myriadrf/front-end-modules/LimeSDR_PA_LNA/hardware/v1r3/KiCAD/Analog Circuits.sch

## KiCad design LimeSDR_PA_LNA/hardware/v1r3/KiCAD/Analog Circuits.sch (2016-06-01)

Schematic: Analog Circuits.sch

Parts:
R12: 10K_0402; SMD0402; Manufacturer Part Number RMCF0402FT10K0
R119, R120, R149, R150, R164, R165, R166, R167: 390R_0402; SMD0402; Manufacturer Part Number RMCF0402FT390R
U1: LMS7002; aQFN-261
X8, X9, X10, X11, X12, X13, X14, X15, X16, X17, X18, X19, X20, X21, X22, X23, X24, X25, X26, X27, X28, X29, X30, X31: U.FL; Manufacturer Part Number 0734120110
