myriadrf/front-end-modules/LimeSDR_PA_LNA/hardware/v1r3/KiCAD/Digital Circuits.sch

## KiCad design LimeSDR_PA_LNA/hardware/v1r3/KiCAD/Digital Circuits.sch (2016-06-01)

Schematic: Digital Circuits.sch

Parts:
C29, C161, C163: 1UF_0402; SMD0402; Manufacturer Part Number CC0402ZRY5V5BB105
C37: 100NF_0402; SMD0402; Manufacturer Part Number CC0402ZRY5V7BB104
C38: 100PF_0402; SMD0402; Manufacturer Part Number CC0402JRNPO9BN101
C119: 10PF_0402; SMD0402; Manufacturer Part Number CC0402JRNPO9BN100
C236, C237: 47PF_0402; SM0402; Manufacturer Part Number CC0402JRNPO9BN470
J1: FX10A-80P8; Manufacturer Part Number FX10B-80P/8-SV1(71)
J3: PINHEADER_2X5_TH; Pinhead_2x5_TH; Manufacturer Part Number 67996-412HLF
R9, R36, R63, R64, R65, R66: 47R_0402; SMD0402; Manufacturer Part Number RC0402FR-0747RL
R13, R37, R72: 10K_0402; SMD0402; Manufacturer Part Number RMCF0402FT10K0
R35, R38, R49: 0R_0402_NF; R_SM0402; Manufacturer Part Number RC0402JR-070RL
R39, R41, R42: 0R_0402; SMD0402; Manufacturer Part Number RC0402JR-070RL
R40, R44: 2K2_0402; SMD0402; Manufacturer Part Number RC0402FR-072K2L
TP1: TP
U1: LMS7002; aQFN-261
U2: CDCV304PWR; TSSOP-8; Manufacturer Part Number CDCV304PWR
U22: 24FC64F; 8-TSSOP; Manufacturer Part Number 24FC64F-I/ST
U23: 24FC512; 8-TSSOP; Manufacturer Part Number 24FC512-I/ST

Notes on the sheet:
+5V
