myriadrf/front-end-modules/LimeSDR_PA_LNA/hardware/v1r3/KiCAD/LMS7002 Power Supply.sch

## KiCad design LimeSDR_PA_LNA/hardware/v1r3/KiCAD/LMS7002 Power Supply.sch (2016-06-01)

Schematic: LMS7002 Power Supply.sch

Parts:
C30, C31, C32, C33, C36, C46, C47, C48, C49, C50, C51, C52, C53, C54, C55, C56, C57, C58, C59, C60, C62, C180, C181, C182, C183, C184, C185, C186, C188, C190, C192, C194, C220, C221, C222, C223, C224, C225: 1UF_0201; SM0201; Manufacturer Part Number C0603X5R0J105M030BC
FB1, FB2, FB3, FB4, FB5, FB6, FB7, FB8, FB10, FB11, FB12, FB13, FB14, FB22, FB28, FB30, FB32, FB34, FB36: FB_0201; SM0201; Manufacturer Part Number BK0603TS601-T
R2, R23, R146, R147, R148, R186: 0R_0201; SMD0201; Manufacturer Part Number MCR006YRTJ000
R48, R50: 0R_0402_NF; R_SM0402; Manufacturer Part Number RC0402JR-070RL
R61, R67, R68, R69, R70, R71: 10R_0201; SMD0201; Manufacturer Part Number RC0201JR-0710RP
R171, R172: 0.22R_0402; SMD0402; Manufacturer Part Number RL0402FR-070R22L
U1: LMS7002; aQFN-261
