myriadrf/front-end-modules/LimeSDR_PA_LNA/hardware/v1r3/KiCAD/Microcontroller.sch

## KiCad design LimeSDR_PA_LNA/hardware/v1r3/KiCAD/Microcontroller.sch (2016-06-01)

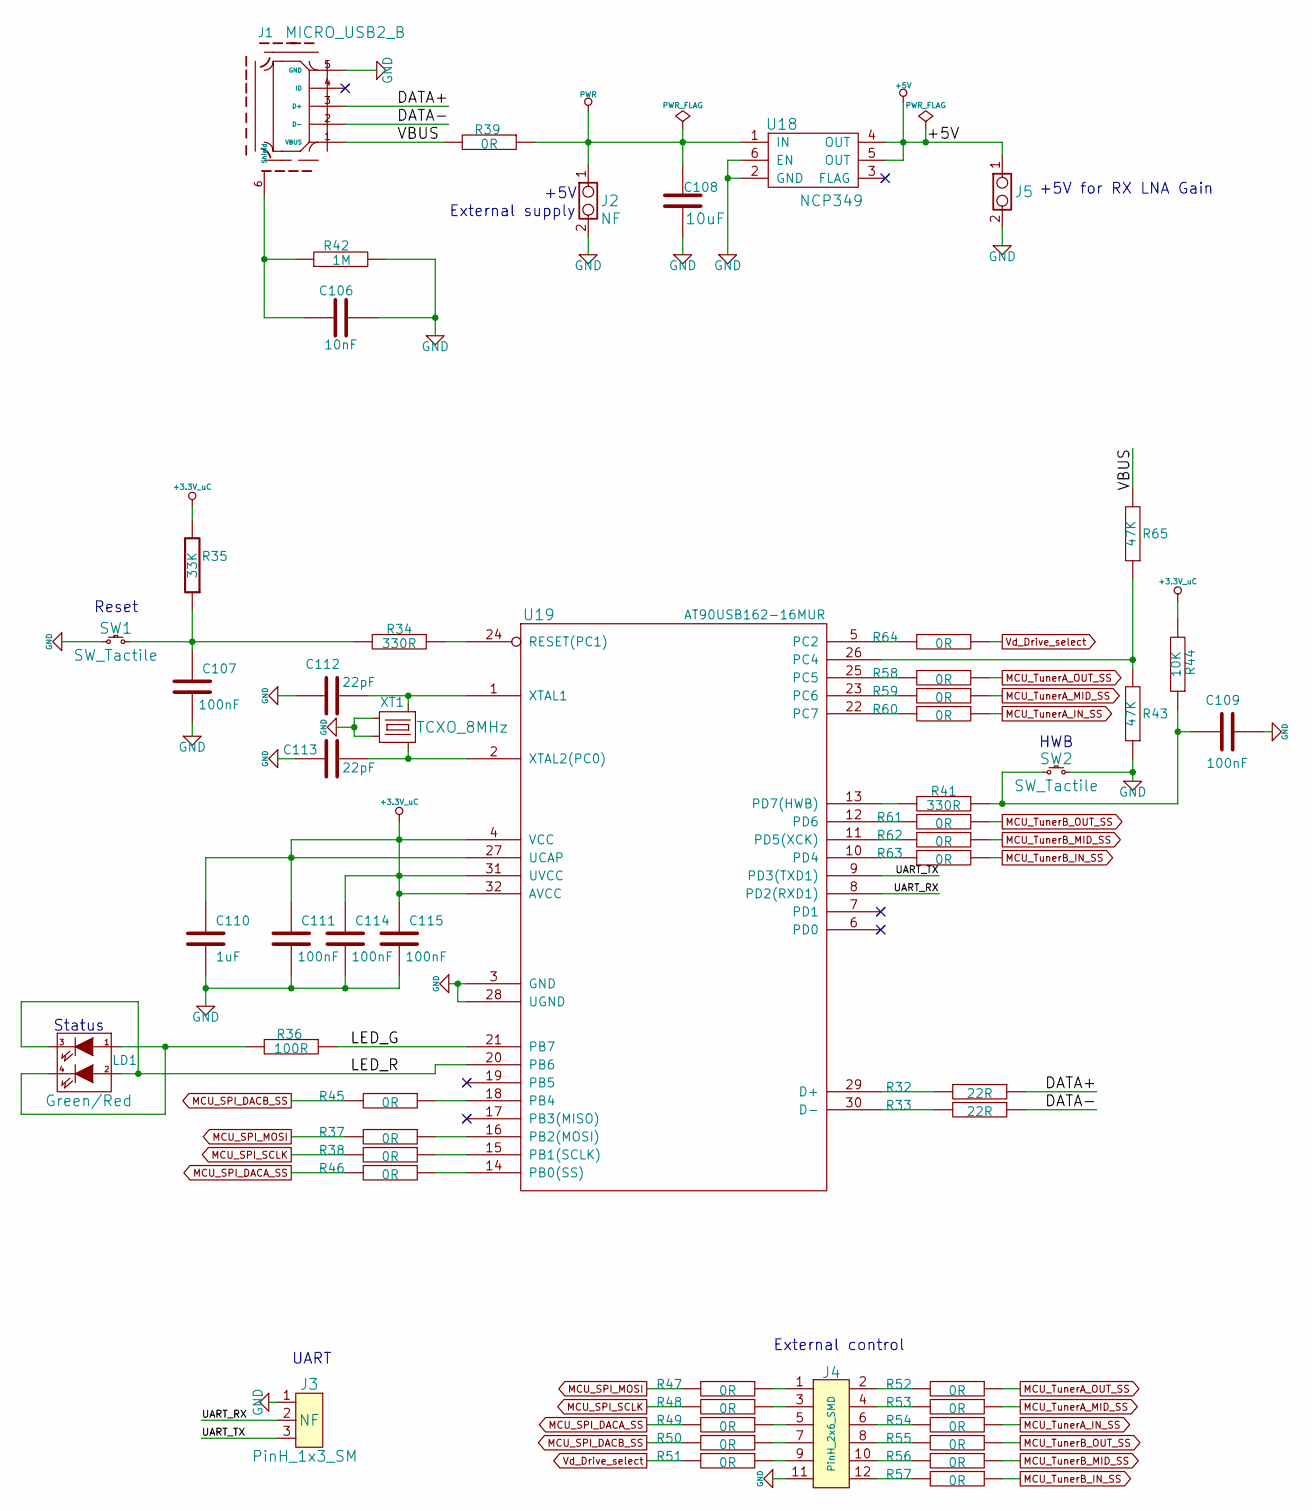
[picture p31: schematic Microcontroller.sch]

Parts:
C106: 10nF_0402; SM0402; Manufacturer Part Number CC0402KRX7R9BB103
C107, C109, C111, C114, C115: 100NF_0402; SMD0402; Manufacturer Part Number CC0402ZRY5V7BB104
C108: 10UF_1206; SMD1206; Manufacturer Part Number CC1206ZKY5V7BB106
C110: 1uF_0402; SMD0402; Manufacturer Part Number CC0402ZRY5V5BB105
C112, C113: 22pF_0402; SMD0402; Manufacturer Part Number CC0402JRNPO9BN220
J1: MICRO_USB2_B; microUSB2; Manufacturer Part Number 10118193-0001LF
J2: pinhead_2_NF; pinhead2; Manufacturer Part Number 5-146285-2
J3: PINHEADER_1X3_SM; Pinhead_1x3_SM; Manufacturer Part Number GRPB031VWTC-RC
J4: Pinheader_2x6_SMD_1.27; Pinhead_2x6_SMD; Manufacturer Part Number M50-3600642
J5: pinhead_2; pinhead2; Manufacturer Part Number 5-146285-2
LD1: LED_0603_GR; LD_0603; Manufacturer Part Number HSMF-C165
R32, R33: 22R_0402; SMD0402; Manufacturer Part Number RC0402JR-0722RL
R34, R41: 330R_0402; SMD0402; Manufacturer Part Number RC0402JR-07330RL
R35: 33K_0402; R_SM0402; Manufacturer Part Number RC0402FR-0733KL
R36: 100R_0402; SMD0402; Manufacturer Part Number RC0603JR-07100RL
R37, R38, R39, R45, R46, R47, R48, R49, R50, R51, R52, R53, R54, R55, R56, R57, R58, R59, R60, R61, R62, R63, R64: 0R_0402; SMD0402; Manufacturer Part Number RC0402JR-070RL
R42: 1M_0402; R_SM0402; Manufacturer Part Number RC0402FR-071ML
R43, R65: 47K_0402; SMD0402; Manufacturer Part Number RC0402FR-0747KL
R44: 10K_0402; SMD0402; Manufacturer Part Number RMCF0402FT10K0
SW1, SW2: SW_Tactile; SW_B3U-1000P; Manufacturer Part Number B3U-1000P
U18: NCP349; 6-DFN; Manufacturer Part Number NCP349MNAETBG
U19: AT90USB162-16MUR; VQFN32; Manufacturer Part Number AT90USB162-16MUR
XT1: TCXO_8MHz; XO_4DFN; Manufacturer Part Number ABM3B-8.000MHZ-B2-T

Connections:
+3.3V_uC: C110.1, C111.1, C114.1, C115.1, R35.2, R44.2, U19.4 (VCC), U19.27 (UCAP), U19.31 (UVCC), U19.32 (AVCC)
+5V: J5.1, U18.4 (OUT), U18.5 (OUT)
DATA+: J1.3 (D+), R32.1
DATA-: J1.2 (D-), R33.1
GND: C106.2, C107.2, C108.2, C109.2, C110.2, C111.2, C112.1, C113.1, C114.2, C115.2, J1.5 (GND), J2.2, J3.1, J4.11, J5.2, R42.2, R43.1, SW1.1 (Base), SW2.2 (Coll), U18.2 (GND), U18.6 (EN), U19.3 (GND), U19.28 (UGND), XT1.2, XT1.4
LED_G: R36.1, U19.21 (PB7)
LED_R: LD1.2 (A), LD1.3 (K), U19.20 (PB6)
MCU_SPI_DACA_SS: R46.2, R49.2
MCU_SPI_DACB_SS: R45.2, R50.2
MCU_SPI_MOSI: R37.2, R47.2
MCU_SPI_SCLK: R38.2, R48.2
MCU_TunerA_IN_SS: R54.1, R60.1
MCU_TunerA_MID_SS: R53.1, R59.1
MCU_TunerA_OUT_SS: R52.1, R58.1
MCU_TunerB_IN_SS: R57.1, R63.1
MCU_TunerB_MID_SS: R56.1, R62.1
MCU_TunerB_OUT_SS: R55.1, R61.1
unnamed: C106.1, J1.6 (Shield), R42.1
unnamed: C107.1, R34.2, R35.1, SW1.2 (Coll)
unnamed: C109.1, R41.1, R44.1, SW2.1 (Base)
unnamed: C112.2, U19.1 (XTAL1), XT1.3
unnamed: C113.2, U19.2 (XTAL2(PC0)), XT1.1
unnamed: J4.1, R47.1
unnamed: J4.2, R52.2
unnamed: J4.3, R48.1
unnamed: J4.4, R53.2
unnamed: J4.5, R49.1
unnamed: J4.6, R54.2
unnamed: J4.7, R50.1
unnamed: J4.8, R55.2
unnamed: J4.9, R51.1
unnamed: J4.10, R56.2
unnamed: J4.12, R57.2
unnamed: LD1.1 (A), LD1.4 (K), R36.2
unnamed: R32.2, U19.29 (D+)
unnamed: R33.2, U19.30 (D-)
unnamed: R34.1, U19.24 (RESET(PC1))
unnamed: R37.1, U19.16 (PB2(MOSI))
unnamed: R38.1, U19.15 (PB1(SCLK))
unnamed: R41.2, U19.13 (PD7(HWB))
unnamed: R43.2, R65.1, U19.26 (PC4)
unnamed: R45.1, U19.18 (PB4)
unnamed: R46.1, U19.14 (PB0(SS))
unnamed: R58.2, U19.25 (PC5)
unnamed: R59.2, U19.23 (PC6)
unnamed: R60.2, U19.22 (PC7)
unnamed: R61.2, U19.12 (PD6)
unnamed: R62.2, U19.11 (PD5(XCK))
unnamed: R63.2, U19.10 (PD4)
unnamed: R64.2, U19.5 (PC2)
PWR: C108.1, J2.1, R39.1, U18.1 (IN)
UART_RX: J3.2, U19.8 (PD2(RXD1))
UART_TX: J3.3, U19.9 (PD3(TXD1))
VBUS: J1.1 (VBUS), R39.2, R65.2
Vd_Drive_select: R51.2, R64.1

Notes on the sheet:
+5V
Status
External control
External supply
UART
Reset
+5V for RX LNA Gain
HWB
