myriadrf/front-end-modules/LimeSDR_PA_LNA/hardware/v1r3/KiCAD/Power Supply.sch

## KiCad design LimeSDR_PA_LNA/hardware/v1r3/KiCAD/Power Supply.sch (2016-06-01)

Schematic: Power Supply.sch

Parts:
C9, C10, C11, C12, C13, C14, C16, C18, C24, C29: 1UF_0402; SMD0402; Manufacturer Part Number CC0402ZRY5V5BB105
C15, C23: 10UF_0402; SMD0402; Manufacturer Part Number CL05A106MP5NUNC
C17, C25, C28: 100NF_0402; SMD0402; Manufacturer Part Number CC0402ZRY5V7BB104
C19, C20, C21, C22, C26, C27, C30, C31: 2.2UF_0603; SMD0603; Manufacturer Part Number CC0603ZRY5V6BB225
FB1, FB2, FB3: FB_60R_0805; FB_SM0805; Manufacturer Part Number MMZ2012Y600B
FD1, FD2, FD3, FD4, FD5, FD6: FIDUCIAL; Fiducial
R1, R10, R22: 10K_0402; SMD0402; Manufacturer Part Number RMCF0402FT10K0
R2, R6: 200R_0402; R_SM0402; Manufacturer Part Number RC0402FR-07200RL
R3, R4, R23: 1K_0402; SMD0402; Manufacturer Part Number RMCF0402FT1K00
R5, R11, R12, R13, R20, R30: 0R_0402; SM0402; Manufacturer Part Number CRCW04020000Z0ED
R7, R8: 2K32_0402; SM0402; Manufacturer Part Number RMCF0402FT2K32
R9, R21: 0R_0402_NF; R_SM0402; Manufacturer Part Number RC0402JR-070RL
R14, R15, R16, R25, R26, R27: 15K_0402; R_SM0402; Manufacturer Part Number RC0402FR-0715KL
R17, R18, R19, R28, R29, R31: 4K3_0402; R_SM0402; Manufacturer Part Number RC0402JR-074K3L
R24: 806R_0402; SM0402; Manufacturer Part Number RMCF0402FT806R
U3, U7: AD5601B; SC-70-6; Manufacturer Part Number AD5601BKSZ-REEL7
U4, U5, U6, U8: MIC37122YMT_ADJ_6TMLF; 6TMLF; Manufacturer Part Number MIC37122YMT-TR
U9: POWERSWITCH_2:1; 6-UFBGA; Manufacturer Part Number FPF1320UCX

Notes on the sheet:
(3.3V)
VDAC_A - Vg_A 1.13V - 0.25V 1.55V - 0.35V 2.00V - 0.45V
Vd Drive - VOUT 0 - 5V 1 - 2V
VDAC_B - Vg _B 1.13V - 0.25V 1.55V - 0.35V 2.00V - 0.45V
VDAC_A
VDAC_B
