myriadrf/front-end-modules/LimeSDR_PA_LNA/hardware/v1r3/KiCAD/RF1.sch

## KiCad design LimeSDR_PA_LNA/hardware/v1r3/KiCAD/RF1.sch (2016-06-01)

Schematic: RF1.sch

Parts:
C1, C9, C10, C11, C13, C121, C166: 100NF_0402; SMD0402; Manufacturer Part Number CC0402ZRY5V7BB104
C2, C7, C20, C24, C34: 1PF_0402; SMD0402; Manufacturer Part Number C1005C0G1H010B050BA
C3, C21: 100PF_0402; SMD0402; Manufacturer Part Number CC0402JRNPO9BN101
C6, C35, C235: 0.5PF_0402_NF; SMD0402; Manufacturer Part Number CC0402CRNPO9BNR50
C12: 1PF_0402_NF; SMD0402; Manufacturer Part Number C1005C0G1H010B050BA
C14, C18, C26, C27: 220PF_0402; SMD0402; Manufacturer Part Number CC0402KRX7R9BB221
C15, C28: 470PF_0402; SMD0402; Manufacturer Part Number C1005C0G1H471J050BA
C67, C69: 1.5PF_0402; SMD0402; Manufacturer Part Number C1005C0G1H1R5B050BA
C68: 0.5PF_0402; SMD0402; Manufacturer Part Number CC0402CRNPO9BNR50
L1, L2, L9: 8.2NH_0402; IND_0402; Manufacturer Part Number 0402HP-8N2XJLU
L6, L7: 270NH_0402; IND_0402; Manufacturer Part Number 0402HL-271XJRU
L13: 12NH_0402_NF; IND_0402; Manufacturer Part Number 0402HP-12NX_LU
L14, L15: 100UH_0805; SM0805; Manufacturer Part Number MLF2012C101K
L17: 4.7NH_0402; IND_0402; Manufacturer Part Number 0402HP-4N7X_LU
T1, T2, T3, T5: TR_TC1; TC1-1-13MA+; Manufacturer Part Number TC1-1-13MA+
T4: TR_TCM1-43X+; TCM1-43X+; Manufacturer Part Number TCM1-43X+
U1: LMS7002; aQFN-261; Manufacturer Part Number LMS7002M

Notes on the sheet:
LNAW_A
LNAL_A
LNAH_A
TX2_A
TX1_A
Broadband
High Band
Low Band
Broadband
