myriadrf/front-end-modules/LimeSDR_PA_LNA/hardware/v1r3/KiCAD/RF2.sch

## KiCad design LimeSDR_PA_LNA/hardware/v1r3/KiCAD/RF2.sch (2016-06-01)

Schematic: RF2.sch

Parts:
C4, C5, C8, C16, C25, C45, C86: 100NF_0402; SMD0402; Manufacturer Part Number CC0402ZRY5V7BB104
C17: 1PF_0402_NF; SMD0402; Manufacturer Part Number C1005C0G1H010B050BA
C19, C82, C238: 0.5PF_0402_NF; SMD0402; Manufacturer Part Number CC0402CRNPO9BNR50
C22, C23, C74, C78, C81: 1PF_0402; SMD0402; Manufacturer Part Number C1005C0G1H010B050BA
C72, C73, C79, C80: 220PF_0402; SMD0402; Manufacturer Part Number CC0402KRX7R9BB221
C83, C85: 1.5PF_0402; SMD0402; Manufacturer Part Number C1005C0G1H1R5B050BA
C84: 0.5PF_0402; SMD0402; Manufacturer Part Number CC0402CRNPO9BNR50
C87, C89: 100PF_0402; SMD0402; Manufacturer Part Number CC0402JRNPO9BN101
C88, C90: 470PF_0402; SMD0402; Manufacturer Part Number C1005C0G1H471J050BA
L3, L5, L10: 8.2NH_0402; IND_0402; Manufacturer Part Number 0402HP-8N2XJLU
L4, L8: 270NH_0402; IND_0402; Manufacturer Part Number 0402HL-271XJRU
L11: 12NH_0402_NF; IND_0402; Manufacturer Part Number 0402HP-12NX_LU
L12: 4.7NH_0402; IND_0402; Manufacturer Part Number 0402HP-4N7X_LU
L16, L18: 100UH_0805; SM0805; Manufacturer Part Number MLF2012C101K
T6, T7, T8, T10: TR_TC1; TC1-1-13MA+; Manufacturer Part Number TC1-1-13MA+
T9: TR_TCM1-43X+; TCM1-43X+; Manufacturer Part Number TCM1-43X+
U1: LMS7002; aQFN-261

Notes on the sheet:
LNAW_B
LNAL_B
LNAH_B
TX2_B
TX1_B
Broadband
High Band
Low Band
Broadband
Low Band
