myriadrf/front-end-modules/LimeSDR_PA_LNA/hardware/v1r3/KiCAD/RX_LNA chain.sch

## KiCad design LimeSDR_PA_LNA/hardware/v1r3/KiCAD/RX_LNA chain.sch (2016-06-01)

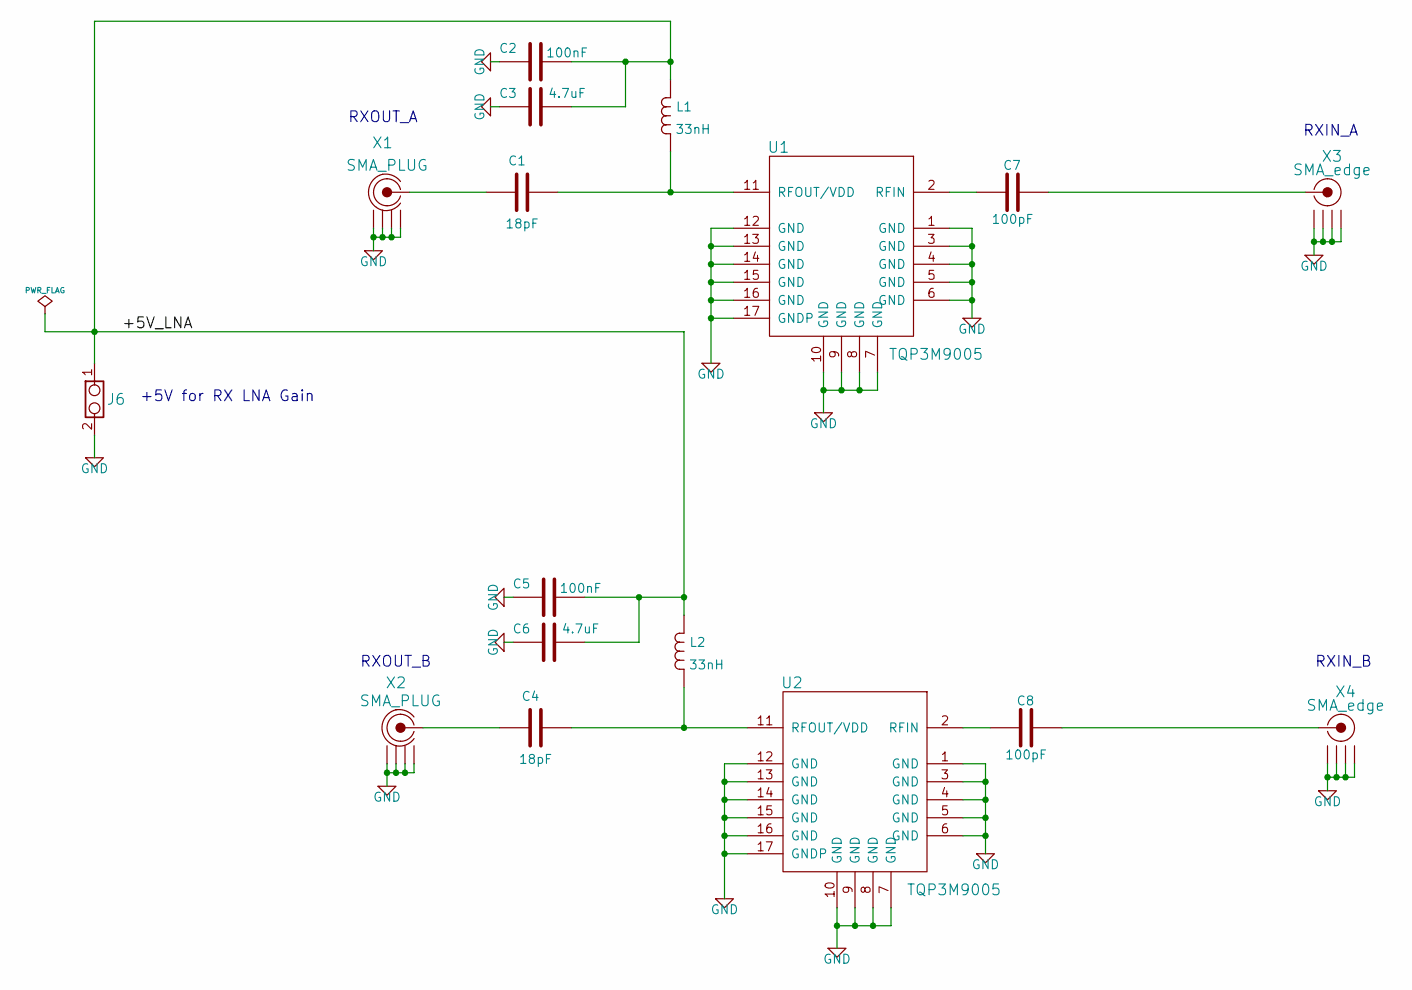
[picture p32: schematic RX_LNA chain.sch]

Parts:
C1, C4: 18PF_0402; SM0402; Manufacturer Part Number CC0402JRNPO9BN180
C2, C5: 100NF_0402; SMD0402; Manufacturer Part Number CC0402ZRY5V7BB104
C3, C6: 4.7UF_0402; SM0402; Manufacturer Part Number C1005X5R0J475M050BC
C7, C8: 100PF_0402; SMD0402; Manufacturer Part Number CC0402JRNPO9BN101
J6: pinhead_2; pinhead2; Manufacturer Part Number 5-146285-2
L1, L2: 33NH_0402; SM0402; Manufacturer Part Number 0402CS-33NX_LU
U1, U2: TQP3M9005; QFN16_LNA; Manufacturer Part Number TQP3M9005
X1, X2: SMA_PLUG; SMA; Manufacturer Part Number CONSMA013.062
X3, X4: SMA_edge; Manufacturer Part Number 142-0711-821

Connections:
+5V_LNA: C2.2, C3.2, C5.2, C6.2, J6.1, L1.1, L2.1
GND: C2.1, C3.1, C5.1, C6.1, J6.2, U1.1 (GND), U1.3 (GND), U1.4 (GND), U1.5 (GND), U1.6 (GND), U1.7 (GND), U1.8 (GND), U1.9 (GND), U1.10 (GND), U1.12 (GND), U1.13 (GND), U1.14 (GND), U1.15 (GND), U1.16 (GND), U1.17 (GNDP), U2.1 (GND), U2.3 (GND), U2.4 (GND), U2.5 (GND), U2.6 (GND), U2.7 (GND), U2.8 (GND), U2.9 (GND), U2.10 (GND), U2.12 (GND), U2.13 (GND), U2.14 (GND), U2.15 (GND), U2.16 (GND), U2.17 (GNDP), X1.2 (GND1), X1.3 (GND2), X1.4 (GND3), X1.5 (GND4), X2.2 (GND1), X2.3 (GND2), X2.4 (GND3), X2.5 (GND4), X3.2 (GND1), X3.3 (GND2), X3.4 (GND3), X3.5 (GND4), X4.2 (GND1), X4.3 (GND2), X4.4 (GND3), X4.5 (GND4)
unnamed: C1.1, X1.1 (RF)
unnamed: C1.2, L1.2, U1.11 (RFOUT/VDD)
unnamed: C4.1, X2.1 (RF)
unnamed: C4.2, L2.2, U2.11 (RFOUT/VDD)
unnamed: C7.1, U1.2 (RFIN)
unnamed: C7.2, X3.1 (RF)
unnamed: C8.1, U2.2 (RFIN)
unnamed: C8.2, X4.1 (RF)

Notes on the sheet:
RXOUT_A
RXOUT_B
RXIN_A
RXIN_B
+5V for RX LNA Gain
