myriadrf/front-end-modules/LimeSDR_PA_LNA/hardware/v1r3/KiCAD/TX_A PA chain.sch

## KiCad design LimeSDR_PA_LNA/hardware/v1r3/KiCAD/TX_A PA chain.sch (2016-06-01)

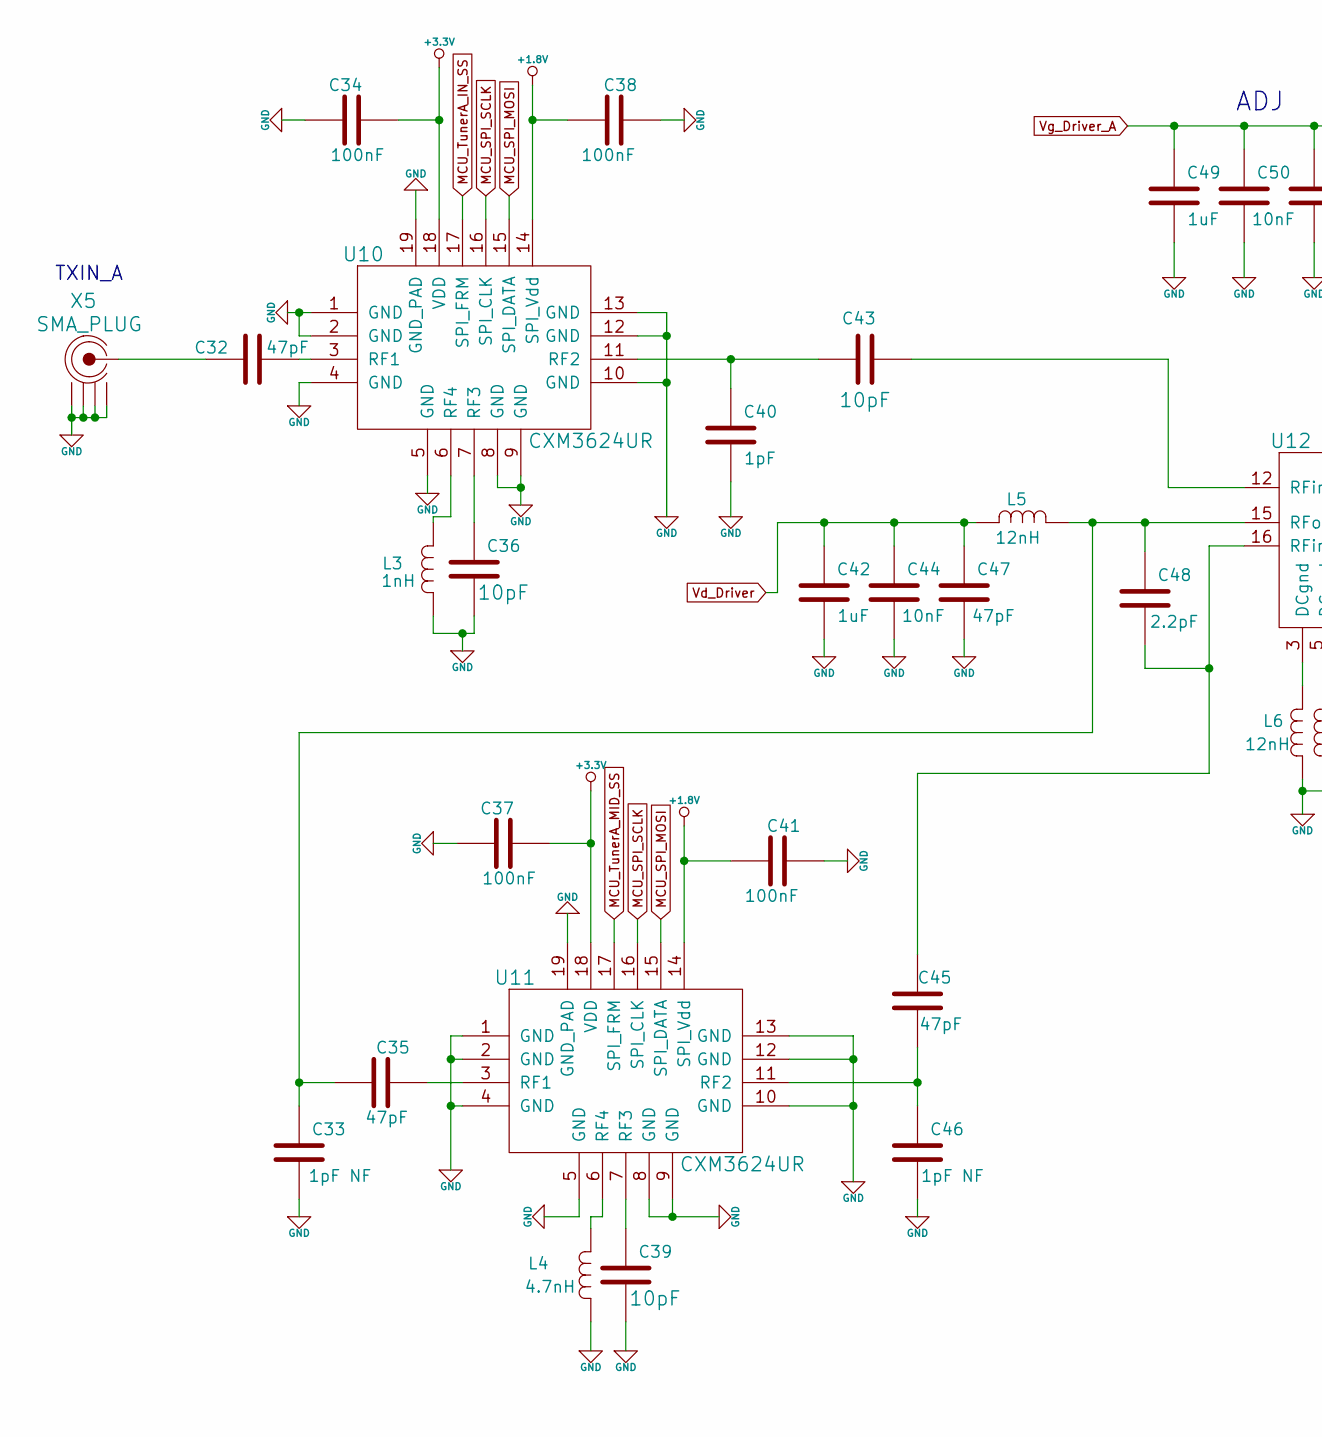
[picture p33: schematic TX_A PA chain.sch, part in row 1, column 1]

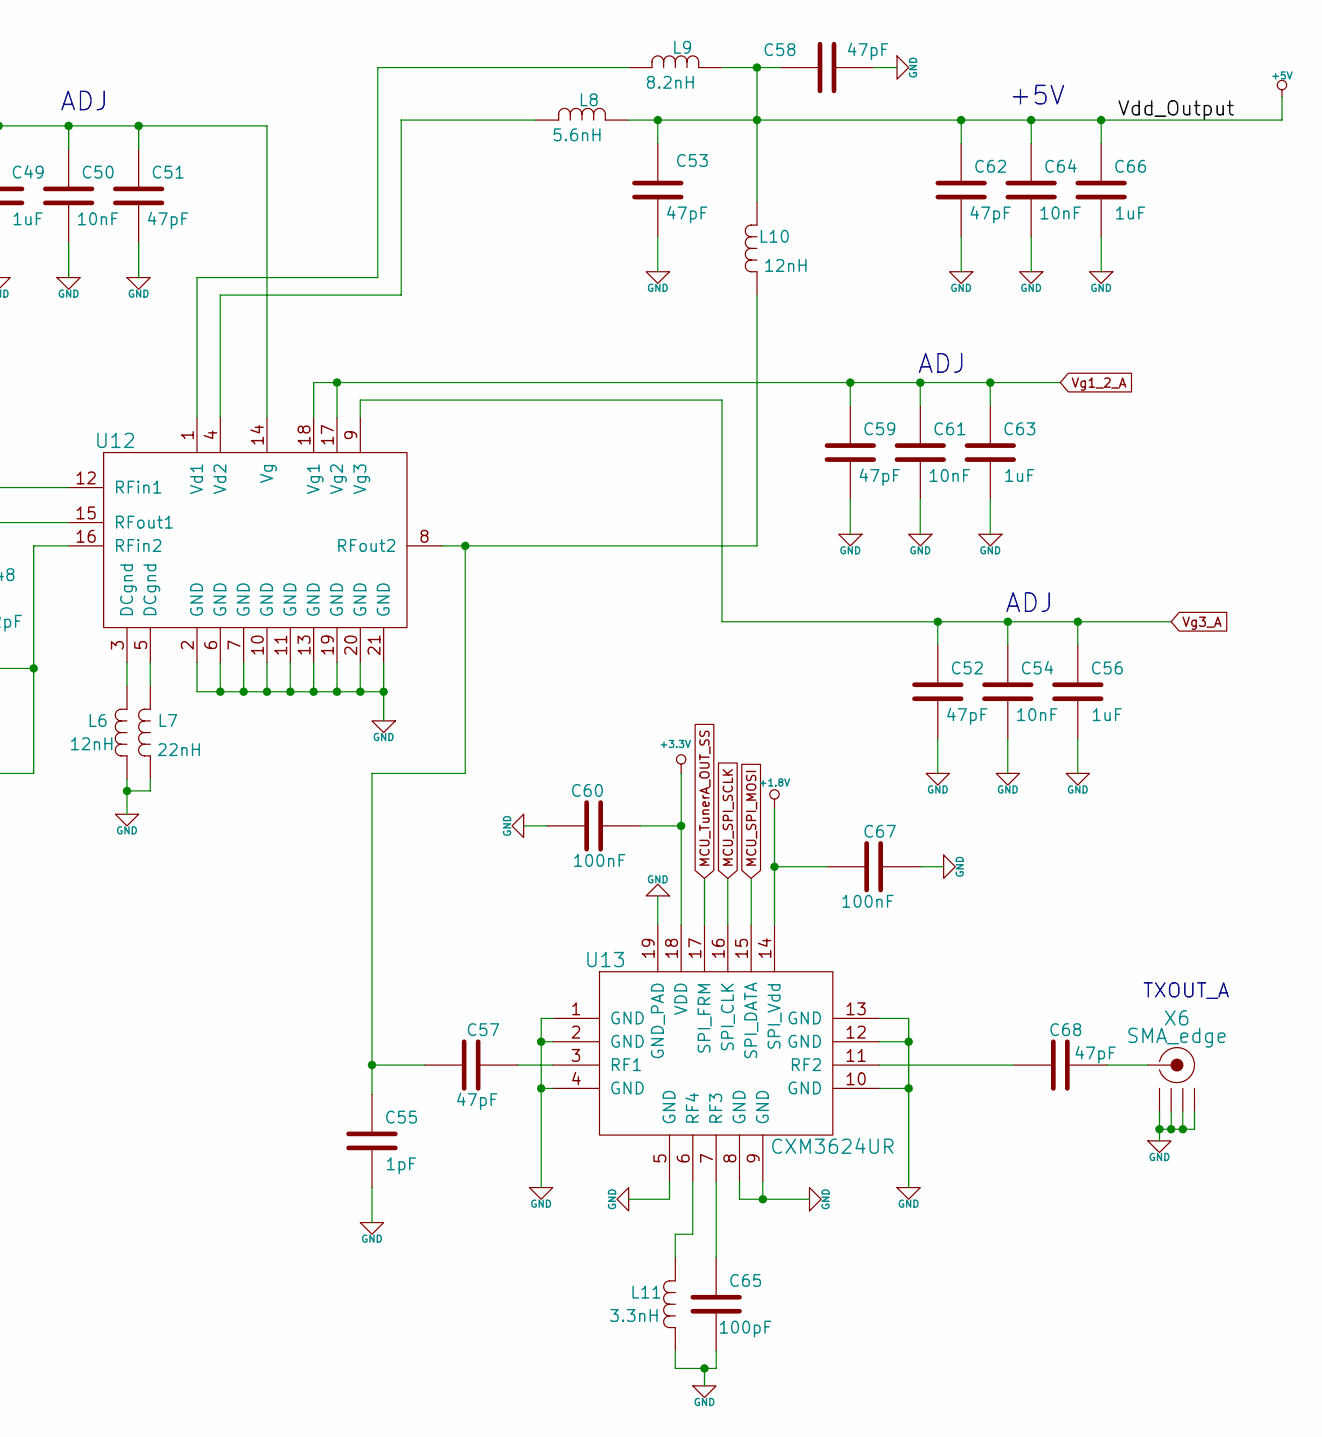
[picture p34: schematic TX_A PA chain.sch, part in row 1, column 2]

Parts:
C32, C35, C47, C51, C52, C53, C57, C58, C59, C62, C68: 47PF_0402; SM0402; Manufacturer Part Number CC0402JRNPO9BN470
C33, C46: 1PF_0402_NF; SMD0402; Manufacturer Part Number C1005C0G1H010B050BA
C34, C37, C38, C41, C60, C67: 100NF_0402; SMD0402; Manufacturer Part Number CC0402ZRY5V7BB104
C36, C39, C43: 10pF_0402; SMD0402; Manufacturer Part Number CC0402JRNPO9BN100
C40, C55: 1PF_0402; SMD0402; Manufacturer Part Number C1005C0G1H010B050BA
C42, C49, C56, C63, C66: 1UF_0402; SMD0402; Manufacturer Part Number CC0402ZRY5V5BB105
C44, C50, C54, C61, C64: 10NF_0402; SM0402; Manufacturer Part Number CC0402KRX7R9BB103
C45: 47pF_0402; SM0402; Manufacturer Part Number CC0402JRNPO9BN470
C48: 2.2pF_0402; SMD0402; Manufacturer Part Number C1005NP01H2R2C050BA
C65: 100pF_0402; SMD0402; Manufacturer Part Number CC0402JRNPO9BN101
L3: 1.0nH_0402; L_SM0402; Manufacturer Part Number 0402HP-1N0XJLU
L4: 4.7NH_0402; IND_0402; Manufacturer Part Number 0402HP-4N7X_LU
L5, L6, L10: 12NH_0402; SM0402; Manufacturer Part Number 0402HP-12NX_LU
L7: 22NH_0402; L_SM0402; Manufacturer Part Number 0402HP-22NX_LU
L8: 5.6NH_0402; L_SM0402; Manufacturer Part Number 0402HP-5N6XJLU
L9: 8.2NH_0402; IND_0402; Manufacturer Part Number 0402HP-8N2X_LU
L11: 3.3nH_0402; L_SM0402; Manufacturer Part Number 0402HP-3N3X_LU
U10, U11, U13: CXM3624UR; UQFN_18P; Manufacturer Part Number CXM3624UR
U12: CXGXXXX; 20PIN-VQFN
X5: SMA_PLUG; SMA; Manufacturer Part Number CONSMA013.062
X6: SMA_edge; Manufacturer Part Number 142-0711-821

Connections:
+1.8V: C38.2, C41.2, C67.2, U10.14 (SPI_Vdd), U11.14 (SPI_Vdd), U13.14 (SPI_Vdd)
+3.3V: C34.2, C37.2, C60.2, U10.18 (VDD), U11.18 (VDD), U13.18 (VDD)
+5V: C53.2, C58.1, C62.1, C64.1, C66.1, L8.1, L9.1, L10.1
GND: C33.2, C34.1, C36.2, C37.1, C38.1, C39.2, C40.2, C41.1, C42.2, C44.2, C46.2, C47.2, C49.2, C50.2, C51.2, C52.2, C53.1, C54.2, C55.2, C56.2, C58.2, C59.2, C60.1, C61.2, C62.2, C63.2, C64.2, C65.2, C66.2, C67.1, L3.2, L4.2, L6.2, L7.2, L11.2, U10.1 (GND), U10.2 (GND), U10.4 (GND), U10.5 (GND), U10.8 (GND), U10.9 (GND), U10.10 (GND), U10.12 (GND), U10.13 (GND), U10.19 (GND_PAD), U11.1 (GND), U11.2 (GND), U11.4 (GND), U11.5 (GND), U11.8 (GND), U11.9 (GND), U11.10 (GND), U11.12 (GND), U11.13 (GND), U11.19 (GND_PAD), U12.2 (GND), U12.6 (GND), U12.7 (GND), U12.10 (GND), U12.11 (GND), U12.13 (GND), U12.19 (GND), U12.20 (GND), U12.21 (GND), U13.1 (GND), U13.2 (GND), U13.4 (GND), U13.5 (GND), U13.8 (GND), U13.9 (GND), U13.10 (GND), U13.12 (GND), U13.13 (GND), U13.19 (GND_PAD), X5.2 (GND1), X5.3 (GND2), X5.4 (GND3), X5.5 (GND4), X6.2 (GND1), X6.3 (GND2), X6.4 (GND3), X6.5 (GND4)
MCU_SPI_MOSI: U10.15 (SPI_DATA), U11.15 (SPI_DATA), U13.15 (SPI_DATA)
MCU_SPI_SCLK: U10.16 (SPI_CLK), U11.16 (SPI_CLK), U13.16 (SPI_CLK)
MCU_TunerA_IN_SS: U10.17 (SPI_FRM)
MCU_TunerA_MID_SS: U11.17 (SPI_FRM)
MCU_TunerA_OUT_SS: U13.17 (SPI_FRM)
unnamed: C32.1, X5.1 (RF)
unnamed: C32.2, U10.3 (RF1)
unnamed: C33.1, C35.2, C48.1, L5.1, U12.15 (RFout1)
unnamed: C35.1, U11.3 (RF1)
unnamed: C36.1, U10.7 (RF3)
unnamed: C39.1, U11.7 (RF3)
unnamed: C40.1, C43.1, U10.11 (RF2)
unnamed: C43.2, U12.12 (RFin1)
unnamed: C45.1, C46.1, U11.11 (RF2)
unnamed: C45.2, C48.2, U12.16 (RFin2)
unnamed: C55.1, C57.2, L10.2, U12.8 (RFout2)
unnamed: C57.1, U13.3 (RF1)
unnamed: C65.1, U13.7 (RF3)
unnamed: C68.1, U13.11 (RF2)
unnamed: C68.2, X6.1 (RF)
unnamed: L3.1, U10.6 (RF4)
unnamed: L4.1, U11.6 (RF4)
unnamed: L6.1, U12.3 (DCgnd)
unnamed: L7.1, U12.5 (DCgnd)
unnamed: L8.2, U12.4 (Vd2)
unnamed: L9.2, U12.1 (Vd1)
unnamed: L11.1, U13.6 (RF4)
Vd_Driver: C42.1, C44.1, C47.1, L5.2
Vg1_2_A: C59.1, C61.1, C63.1, U12.17 (Vg2), U12.18 (Vg1)
Vg3_A: C52.1, C54.1, C56.1, U12.9 (Vg3)
Vg_Driver_A: C49.1, C50.1, C51.1, U12.14 (Vg)

Notes on the sheet:
ADJ
+5V
TXOUT_A
TXIN_A
