myriadrf/front-end-modules/LimeSDR_PA_LNA/hardware/v1r3/KiCAD/TX_B PA chain.sch

## KiCad design LimeSDR_PA_LNA/hardware/v1r3/KiCAD/TX_B PA chain.sch (2016-06-01)

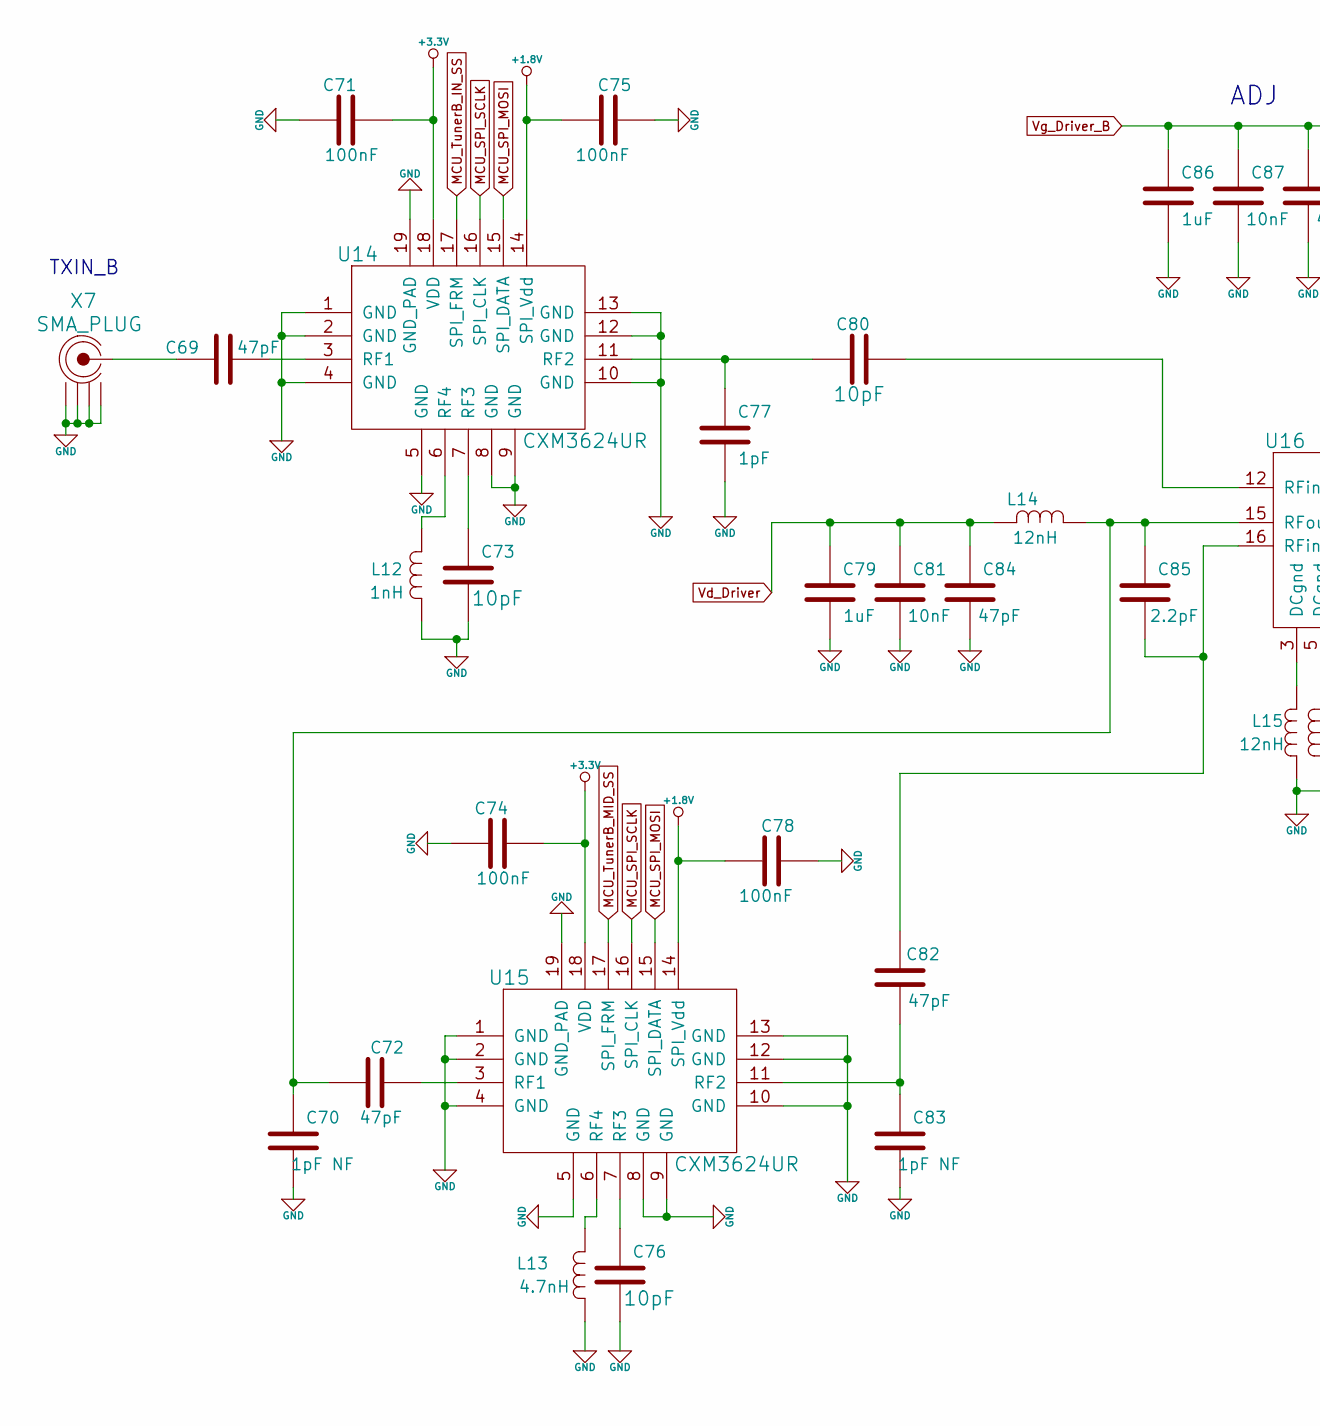
[picture p35: schematic TX_B PA chain.sch, part in row 1, column 1]

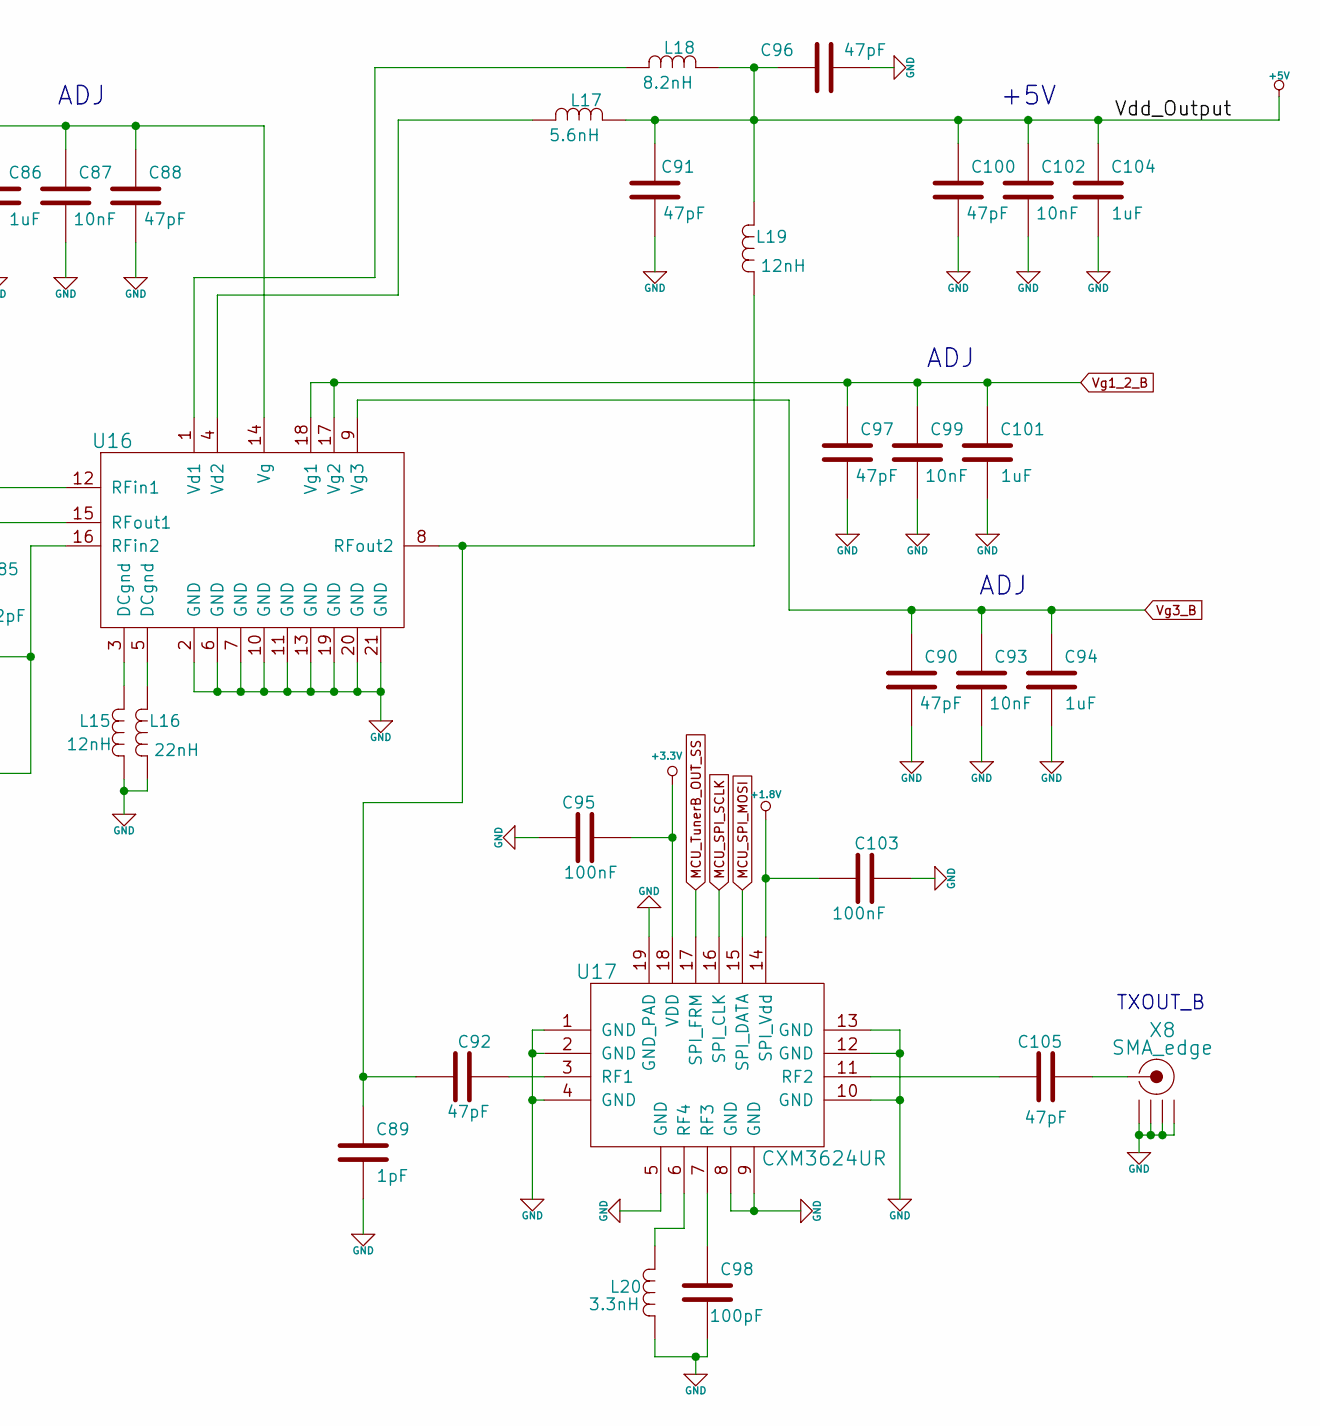
[picture p36: schematic TX_B PA chain.sch, part in row 1, column 2]

Parts:
C69, C72, C84, C88, C90, C91, C92, C96, C97, C100, C105: 47PF_0402; SM0402; Manufacturer Part Number CC0402JRNPO9BN470
C70, C83: 1PF_0402_NF; SMD0402; Manufacturer Part Number C1005C0G1H010B050BA
C71, C74, C75, C78, C95, C103: 100NF_0402; SMD0402; Manufacturer Part Number CC0402ZRY5V7BB104
C73, C76, C80: 10pF_0402; SMD0402; Manufacturer Part Number CC0402JRNPO9BN100
C77, C89: 1PF_0402; SMD0402; Manufacturer Part Number C1005C0G1H010B050BA
C79, C86, C94, C101, C104: 1UF_0402; SMD0402; Manufacturer Part Number CC0402ZRY5V5BB105
C81, C87, C93, C99, C102: 10NF_0402; SM0402; Manufacturer Part Number CC0402KRX7R9BB103
C82: 47pF_0402; SM0402; Manufacturer Part Number CC0402JRNPO9BN470
C85: 2.2pF_0402; SMD0402; Manufacturer Part Number C1005NP01H2R2C050BA
C98: 100pF_0402; SMD0402; Manufacturer Part Number CC0402JRNPO9BN101
L12: 1.0nH_0402; L_SM0402; Manufacturer Part Number 0402HP-1N0XJLU
L13: 4.7NH_0402; IND_0402; Manufacturer Part Number 0402HP-4N7X_LU
L14, L15, L19: 12NH_0402; SM0402; Manufacturer Part Number 0402HP-12NX_LU
L16: 22NH_0402; L_SM0402; Manufacturer Part Number 0402HP-22NX_LU
L17: 5.6NH_0402; L_SM0402; Manufacturer Part Number 0402HP-5N6XJLU
L18: 8.2NH_0402; IND_0402; Manufacturer Part Number 0402HP-8N2X_LU
L20: 3.3nH_0402; L_SM0402; Manufacturer Part Number 0402HP-3N3X_LU
U14, U15, U17: CXM3624UR; UQFN_18P; Manufacturer Part Number CXM3624UR
U16: CXGXXXX; 20PIN-VQFN
X7: SMA_PLUG; SMA; Manufacturer Part Number CONSMA013.062
X8: SMA_edge; Manufacturer Part Number 142-0711-821

Connections:
+1.8V: C75.2, C78.2, C103.2, U14.14 (SPI_Vdd), U15.14 (SPI_Vdd), U17.14 (SPI_Vdd)
+3.3V: C71.2, C74.2, C95.2, U14.18 (VDD), U15.18 (VDD), U17.18 (VDD)
+5V: C91.2, C96.1, C100.1, C102.1, C104.1, L17.1, L18.1, L19.1
GND: C70.2, C71.1, C73.2, C74.1, C75.1, C76.2, C77.2, C78.1, C79.2, C81.2, C83.2, C84.2, C86.2, C87.2, C88.2, C89.2, C90.2, C91.1, C93.2, C94.2, C95.1, C96.2, C97.2, C98.2, C99.2, C100.2, C101.2, C102.2, C103.1, C104.2, L12.2, L13.2, L15.2, L16.2, L20.2, U14.1 (GND), U14.2 (GND), U14.4 (GND), U14.5 (GND), U14.8 (GND), U14.9 (GND), U14.10 (GND), U14.12 (GND), U14.13 (GND), U14.19 (GND_PAD), U15.1 (GND), U15.2 (GND), U15.4 (GND), U15.5 (GND), U15.8 (GND), U15.9 (GND), U15.10 (GND), U15.12 (GND), U15.13 (GND), U15.19 (GND_PAD), U16.2 (GND), U16.6 (GND), U16.7 (GND), U16.10 (GND), U16.11 (GND), U16.13 (GND), U16.19 (GND), U16.20 (GND), U16.21 (GND), U17.1 (GND), U17.2 (GND), U17.4 (GND), U17.5 (GND), U17.8 (GND), U17.9 (GND), U17.10 (GND), U17.12 (GND), U17.13 (GND), U17.19 (GND_PAD), X7.2 (GND1), X7.3 (GND2), X7.4 (GND3), X7.5 (GND4), X8.2 (GND1), X8.3 (GND2), X8.4 (GND3), X8.5 (GND4)
MCU_SPI_MOSI: U14.15 (SPI_DATA), U15.15 (SPI_DATA), U17.15 (SPI_DATA)
MCU_SPI_SCLK: U14.16 (SPI_CLK), U15.16 (SPI_CLK), U17.16 (SPI_CLK)
MCU_TunerB_IN_SS: U14.17 (SPI_FRM)
MCU_TunerB_MID_SS: U15.17 (SPI_FRM)
MCU_TunerB_OUT_SS: U17.17 (SPI_FRM)
unnamed: C69.1, X7.1 (RF)
unnamed: C69.2, U14.3 (RF1)
unnamed: C70.1, C72.2, C85.1, L14.1, U16.15 (RFout1)
unnamed: C72.1, U15.3 (RF1)
unnamed: C73.1, U14.7 (RF3)
unnamed: C76.1, U15.7 (RF3)
unnamed: C77.1, C80.1, U14.11 (RF2)
unnamed: C80.2, U16.12 (RFin1)
unnamed: C82.1, C83.1, U15.11 (RF2)
unnamed: C82.2, C85.2, U16.16 (RFin2)
unnamed: C89.1, C92.2, L19.2, U16.8 (RFout2)
unnamed: C92.1, U17.3 (RF1)
unnamed: C98.1, U17.7 (RF3)
unnamed: C105.1, U17.11 (RF2)
unnamed: C105.2, X8.1 (RF)
unnamed: L12.1, U14.6 (RF4)
unnamed: L13.1, U15.6 (RF4)
unnamed: L15.1, U16.3 (DCgnd)
unnamed: L16.1, U16.5 (DCgnd)
unnamed: L17.2, U16.4 (Vd2)
unnamed: L18.2, U16.1 (Vd1)
unnamed: L20.1, U17.6 (RF4)
Vd_Driver: C79.1, C81.1, C84.1, L14.2
Vg1_2_B: C97.1, C99.1, C101.1, U16.17 (Vg2), U16.18 (Vg1)
Vg3_B: C90.1, C93.1, C94.1, U16.9 (Vg3)
Vg_Driver_B: C86.1, C87.1, C88.1, U16.14 (Vg)

Notes on the sheet:
+5V
ADJ
TXOUT_B
TXIN_B
