myriadrf/front-end-modules/LimeSDR_PA_LNA/gui/pa_setup/SISO_Setup_ChA_ChB_v1.ini

[ChA_0.3GHz]
DAC_A=219
DAC_B=0
EB_A_IN=1
EB_A_MID=0
EB_A_OUT=0
EB_B_IN=0
EB_B_MID=0
EB_B_OUT=0
PA=0
SSC1_A_IN=31
SSC1_A_MID=25
SSC1_A_OUT=31
SSC1_B_IN=0
SSC1_B_MID=0
SSC1_B_OUT=0
SSC2_A_IN=0
SSC2_A_MID=0
SSC2_A_OUT=0
SSC2_B_IN=0
SSC2_B_MID=0
SSC2_B_OUT=0
TP_A_IN=1
TP_A_MID=0
TP_A_OUT=0
TP_B_IN=0
TP_B_MID=0
TP_B_OUT=0
[ChA_0.5GHz]
DAC_A=172
DAC_B=0
EB_A_IN=1
EB_A_MID=0
EB_A_OUT=0
EB_B_IN=0
EB_B_MID=0
EB_B_OUT=0
PA=0
SSC1_A_IN=31
SSC1_A_MID=25
SSC1_A_OUT=31
SSC1_B_IN=0
SSC1_B_MID=0
SSC1_B_OUT=0
SSC2_A_IN=0
SSC2_A_MID=0
SSC2_A_OUT=0
SSC2_B_IN=0
SSC2_B_MID=0
SSC2_B_OUT=0
TP_A_IN=1
TP_A_MID=0
TP_A_OUT=0
TP_B_IN=0
TP_B_MID=0
TP_B_OUT=0
[ChA_0.8GHz]
DAC_A=172
DAC_B=0
EB_A_IN=0
EB_A_MID=0
EB_A_OUT=0
EB_B_IN=0
EB_B_MID=0
EB_B_OUT=0
PA=0
SSC1_A_IN=10
SSC1_A_MID=8
SSC1_A_OUT=31
SSC1_B_IN=0
SSC1_B_MID=0
SSC1_B_OUT=0
SSC2_A_IN=3
SSC2_A_MID=0
SSC2_A_OUT=0
SSC2_B_IN=0
SSC2_B_MID=0
SSC2_B_OUT=0
TP_A_IN=0
TP_A_MID=0
TP_A_OUT=0
TP_B_IN=0
TP_B_MID=0
TP_B_OUT=0
[ChA_1.0GHz]
DAC_A=172
DAC_B=0
EB_A_IN=0
EB_A_MID=0
EB_A_OUT=0
EB_B_IN=0
EB_B_MID=0
EB_B_OUT=0
PA=0
SSC1_A_IN=26
SSC1_A_MID=0
SSC1_A_OUT=24
SSC1_B_IN=0
SSC1_B_MID=0
SSC1_B_OUT=0
SSC2_A_IN=0
SSC2_A_MID=3
SSC2_A_OUT=0
SSC2_B_IN=0
SSC2_B_MID=0
SSC2_B_OUT=0
TP_A_IN=0
TP_A_MID=0
TP_A_OUT=0
TP_B_IN=0
TP_B_MID=0
TP_B_OUT=0
[ChA_1.5GHz]
DAC_A=172
DAC_B=0
EB_A_IN=0
EB_A_MID=1
EB_A_OUT=1
EB_B_IN=0
EB_B_MID=0
EB_B_OUT=0
PA=0
SSC1_A_IN=31
SSC1_A_MID=0
SSC1_A_OUT=31
SSC1_B_IN=0
SSC1_B_MID=0
SSC1_B_OUT=0
SSC2_A_IN=14
SSC2_A_MID=0
SSC2_A_OUT=0
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
DAC_B=193
EB_A_IN=0
EB_A_MID=0
EB_A_OUT=0
EB_B_IN=0
EB_B_MID=1
EB_B_OUT=0
PA=0
SSC1_A_IN=0
SSC1_A_MID=0
SSC1_A_OUT=0
SSC1_B_IN=31
SSC1_B_MID=31
SSC1_B_OUT=31
SSC2_A_IN=0
SSC2_A_MID=0
SSC2_A_OUT=0
SSC2_B_IN=1
SSC2_B_MID=8
SSC2_B_OUT=0
TP_A_IN=0
TP_A_MID=0
TP_A_OUT=0
TP_B_IN=0
TP_B_MID=0
TP_B_OUT=0
