myriadrf/front-end-modules/LimeSDR_PA_LNA/gui/pa_setup/MIMO_Setup_ChA_ChB_v1.ini

[ChA&B_0.3GHz]
DAC_A=234
DAC_B=187
EB_A_IN=1
EB_A_MID=0
EB_A_OUT=0
EB_B_IN=1
EB_B_MID=0
EB_B_OUT=0
PA=0
SSC1_A_IN=31
SSC1_A_MID=25
SSC1_A_OUT=31
SSC1_B_IN=31
SSC1_B_MID=31
SSC1_B_OUT=31
SSC2_A_IN=0
SSC2_A_MID=0
SSC2_A_OUT=0
SSC2_B_IN=0
SSC2_B_MID=0
SSC2_B_OUT=0
TP_A_IN=1
TP_A_MID=0
TP_A_OUT=0
TP_B_IN=1
TP_B_MID=0
TP_B_OUT=0
[ChA&B_0.5GHz]
DAC_A=208
DAC_B=255
EB_A_IN=1
EB_A_MID=0
EB_A_OUT=0
EB_B_IN=1
EB_B_MID=0
EB_B_OUT=0
PA=0
SSC1_A_IN=31
SSC1_A_MID=25
SSC1_A_OUT=31
SSC1_B_IN=31
SSC1_B_MID=31
SSC1_B_OUT=31
SSC2_A_IN=0
SSC2_A_MID=0
SSC2_A_OUT=0
SSC2_B_IN=0
SSC2_B_MID=0
SSC2_B_OUT=0
TP_A_IN=1
TP_A_MID=0
TP_A_OUT=0
TP_B_IN=1
TP_B_MID=0
TP_B_OUT=0
[ChA&B_0.8GHz]
DAC_A=242
DAC_B=255
EB_A_IN=0
EB_A_MID=0
EB_A_OUT=0
EB_B_IN=0
EB_B_MID=0
EB_B_OUT=0
PA=0
SSC1_A_IN=10
SSC1_A_MID=8
SSC1_A_OUT=31
SSC1_B_IN=10
SSC1_B_MID=31
SSC1_B_OUT=31
SSC2_A_IN=3
SSC2_A_MID=0
SSC2_A_OUT=0
SSC2_B_IN=0
SSC2_B_MID=0
SSC2_B_OUT=0
TP_A_IN=0
TP_A_MID=0
TP_A_OUT=0
TP_B_IN=0
TP_B_MID=0
TP_B_OUT=0
[ChA&B_1.0GHz]
DAC_A=208
DAC_B=255
EB_A_IN=0
EB_A_MID=0
EB_A_OUT=0
EB_B_IN=0
EB_B_MID=0
EB_B_OUT=0
PA=0
SSC1_A_IN=26
SSC1_A_MID=0
SSC1_A_OUT=24
SSC1_B_IN=31
SSC1_B_MID=14
SSC1_B_OUT=31
SSC2_A_IN=0
SSC2_A_MID=3
SSC2_A_OUT=0
SSC2_B_IN=0
SSC2_B_MID=0
SSC2_B_OUT=0
TP_A_IN=0
TP_A_MID=0
TP_A_OUT=0
TP_B_IN=0
TP_B_MID=0
TP_B_OUT=1
[ChA&B_1.5GHz]
DAC_A=197
DAC_B=227
EB_A_IN=0
EB_A_MID=1
EB_A_OUT=1
EB_B_IN=0
EB_B_MID=0
EB_B_OUT=1
PA=0
SSC1_A_IN=31
SSC1_A_MID=0
SSC1_A_OUT=31
SSC1_B_IN=31
SSC1_B_MID=14
SSC1_B_OUT=31
SSC2_A_IN=14
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
EB_A_IN=0
EB_A_MID=1
EB_A_OUT=0
EB_B_IN=0
EB_B_MID=1
EB_B_OUT=0
PA=0
SSC1_A_IN=31
SSC1_A_MID=31
SSC1_A_OUT=31
SSC1_B_IN=31
SSC1_B_MID=31
SSC1_B_OUT=31
SSC2_A_IN=0
SSC2_A_MID=15
SSC2_A_OUT=0
SSC2_B_IN=1
SSC2_B_MID=8
SSC2_B_OUT=0
TP_A_IN=0
TP_A_MID=0
TP_A_OUT=0
TP_B_IN=0
TP_B_MID=0
TP_B_OUT=0
