myriadrf/front-end-modules/LimeSDR_PA_LNA/gui/src/protocols/LMS64CProtocol.cpp

/**
    @file LMS64CProtocol.cpp
    @author Lime Microsystems
    @brief Implementation of LMS64C protocol.
*/

#include "ErrorReporting.h"
#include "LMS64CProtocol.h"
#include <chrono>
#include <iostream>
#include <assert.h>
#include <math.h>
#include <algorithm>
#include <iso646.h> // alternative operators for visual c++: not, and, or...
#include <ADCUnits.h>
using namespace lime;

//! CMD_LMS7002_RST options
const int LMS_RST_DEACTIVATE = 0;
const int LMS_RST_ACTIVATE = 1;
const int LMS_RST_PULSE = 2;

//! arbitrary spi constants used to dispatch calls
#define LMS7002M_SPI_INDEX 0x10
#define Si5351_I2C_ADDR 0x20
#define ADF4002_SPI_INDEX 0x30

static int convertStatus(const int &status, const LMS64CProtocol::GenericPacket &pkt)
{
    if (status != 0) return ReportError(EIO, GetLastErrorMessage());
    switch (pkt.status)
    {
    case STATUS_COMPLETED_CMD: return 0;
    case STATUS_UNKNOWN_CMD:
        return ReportError(EPROTONOSUPPORT, "unknown lms64c protocol command");
    }
    return ReportError(EPROTO, status2string(pkt.status));
}

LMS64CProtocol::LMS64CProtocol(void)
{
    //set a sane-default for the rate
    _cachedRefClockRate = 61.44e6/2;
}

LMS64CProtocol::~LMS64CProtocol(void)
{
    return;
}

int LMS64CProtocol::DeviceReset(void)
{
    if (not this->IsOpen())
    {
        return ReportError(ENOTCONN, "connection is not open");
    }

    GenericPacket pkt;
    pkt.cmd = CMD_LMS7002_RST;
    pkt.outBuffer.push_back (LMS_RST_PULSE);
    int status = this->TransferPacket(pkt);

    return convertStatus(status, pkt);
}

int LMS64CProtocol::TransactSPI(const int addr, const uint32_t *writeData, uint32_t *readData, const size_t size)
{
    //! TODO
    //! For multi-LMS7002M, RFIC # could be encoded with the slave number
    //! And the index would need to be encoded into the packet as well

    if (not this->IsOpen())
    {
        ReportError(ENOTCONN, "connection is not open");
        return -1;
    }

    //perform spi writes when there is no read data
    if (readData == nullptr) switch(addr)
    {
    case LMS7002M_SPI_INDEX: return this->WriteLMS7002MSPI(writeData, size);
    case ADF4002_SPI_INDEX: return this->WriteADF4002SPI(writeData, size);
    }

    //otherwise perform reads into the provided buffer
    if (readData != nullptr) switch(addr)
    {
    case LMS7002M_SPI_INDEX: return this->ReadLMS7002MSPI(writeData, readData, size);
    case ADF4002_SPI_INDEX: return this->ReadADF4002SPI(writeData, readData, size);
    }

    return ReportError(ENOTSUP, "unknown spi address");
}

int LMS64CProtocol::WriteI2C(const int addr, const std::string &data)
{
    if (not this->IsOpen())
    {
        return ReportError(ENOTCONN, "connection is not open");
    }

    switch(addr)
    {
    case Si5351_I2C_ADDR: return this->WriteSi5351I2C(data);
    }

    return ReportError(ENOTSUP, "unknown i2c address");
}

int LMS64CProtocol::ReadI2C(const int addr, const size_t numBytes, std::string &data)
{
    if (not this->IsOpen())
    {
        return ReportError(ENOTCONN, "connection is not open");
    }

    switch(addr)
    {
    case Si5351_I2C_ADDR: return this->ReadSi5351I2C(numBytes, data);
    }

    return ReportError(ENOTSUP, "unknown i2c address");
}

double LMS64CProtocol::GetReferenceClockRate(void)
{
    return _cachedRefClockRate;
}

void LMS64CProtocol::SetReferenceClockRate(const double rate)
{
    //TODO set the PLL freq

    //stash the actual reference
    _cachedRefClockRate = rate;
}

/***********************************************************************
 * LMS7002M SPI access
 **********************************************************************/
int LMS64CProtocol::WriteLMS7002MSPI(const uint32_t *writeData, const size_t size)
{
    GenericPacket pkt;
    pkt.cmd = CMD_LMS7002_WR;
    for (size_t i = 0; i < size; ++i)
    {
        uint16_t addr = (writeData[i] >> 16) & 0x7fff;
        uint16_t data = writeData[i] & 0xffff;
        pkt.outBuffer.push_back(addr >> 8);
        pkt.outBuffer.push_back(addr & 0xFF);
        pkt.outBuffer.push_back(data >> 8);
        pkt.outBuffer.push_back(data & 0xFF);
    }

    int status = this->TransferPacket(pkt);

    return convertStatus(status, pkt);
}

int LMS64CProtocol::ReadLMS7002MSPI(const uint32_t *writeData, uint32_t *readData, const size_t size)
{
    GenericPacket pkt;
    pkt.cmd = CMD_LMS7002_RD;
    for (size_t i = 0; i < size; ++i)
    {
        uint16_t addr = (writeData[i] >> 16) & 0x7fff;
        pkt.outBuffer.push_back(addr >> 8);
        pkt.outBuffer.push_back(addr & 0xFF);
    }

    int status = this->TransferPacket(pkt);

    const size_t numRead = std::min<size_t>(pkt.inBuffer.size()/4, size);
    for (size_t i = 0; i < numRead; ++i)
    {
        int hi = pkt.inBuffer[4*i + 2];
        int lo = pkt.inBuffer[4*i + 3];
        readData[i] = (hi << 8) | lo;
    }

    return convertStatus(status, pkt);
}

/***********************************************************************
 * Si5351 SPI access
 **********************************************************************/
int LMS64CProtocol::WriteSi5351I2C(const std::string &data)
{
    GenericPacket pkt;
    pkt.cmd = CMD_SI5351_WR;

    for (size_t i = 0; i < data.size(); i++)
    {
        pkt.outBuffer.push_back(data.at(i));
    }

    int status = this->TransferPacket(pkt);
    return convertStatus(status, pkt);
}

int LMS64CProtocol::ReadSi5351I2C(const size_t numBytes, std::string &data)
{
    GenericPacket pkt;
    pkt.cmd = CMD_SI5351_RD;

    int status = this->TransferPacket(pkt);

    for (size_t i = 0; i < data.size(); i++)
    {
        pkt.outBuffer.push_back(data.at(i));
    }

    data.clear();
    for (size_t i = 0; i < pkt.inBuffer.size(); ++i)
    {
        data += pkt.inBuffer[i];
    }

    return convertStatus(status, pkt);
}

/***********************************************************************
 * ADF4002 SPI access
 **********************************************************************/
int LMS64CProtocol::WriteADF4002SPI(const uint32_t *writeData, const size_t size)
{
    GenericPacket pkt;
    pkt.cmd = CMD_ADF4002_WR;

    for (size_t i = 0; i < size; i++)
    {
        pkt.outBuffer.push_back((writeData[i] >> 16) & 0xff);
        pkt.outBuffer.push_back((writeData[i] >> 8) & 0xff);
        pkt.outBuffer.push_back((writeData[i] >> 0) & 0xff);
    }

    int status = this->TransferPacket(pkt);
    return convertStatus(status, pkt);
}

int LMS64CProtocol::ReadADF4002SPI(const uint32_t *writeData, uint32_t *readData, const size_t size)
{
    //TODO
    ReportError(ENOTSUP);
    return -1;
}

/***********************************************************************
 * Board SPI access
 **********************************************************************/
int LMS64CProtocol::WriteRegisters(const uint32_t *addrs, const uint32_t *data, const size_t size)
{
    GenericPacket pkt;
    pkt.cmd = CMD_BRDSPI_WR;
    for (size_t i = 0; i < size; ++i)
    {
        pkt.outBuffer.push_back(addrs[i] >> 8);
        pkt.outBuffer.push_back(addrs[i] & 0xFF);
        pkt.outBuffer.push_back(data[i] >> 8);
        pkt.outBuffer.push_back(data[i] & 0xFF);
    }

    int status = this->TransferPacket(pkt);

    return convertStatus(status, pkt);
}

int LMS64CProtocol::ReadRegisters(const uint32_t *addrs, uint32_t *data, const size_t size)
{
    GenericPacket pkt;
    pkt.cmd = CMD_BRDSPI_RD;
    for (size_t i = 0; i < size; ++i)
    {
        pkt.outBuffer.push_back(addrs[i] >> 8);
        pkt.outBuffer.push_back(addrs[i] & 0xFF);
    }

    int status = this->TransferPacket(pkt);

    const size_t numRead = std::min<size_t>(pkt.inBuffer.size()/4, size);
    for (size_t i = 0; i < numRead; ++i)
    {
        int hi = pkt.inBuffer[4*i + 2];
        int lo = pkt.inBuffer[4*i + 3];
        data[i] = (hi << 8) | lo;
    }

    return convertStatus(status, pkt);
}

/***********************************************************************
 * Device Information
 **********************************************************************/
DeviceInfo LMS64CProtocol::GetDeviceInfo(void)
{
    LMSinfo lmsInfo = this->GetInfo();
    DeviceInfo devInfo;
    devInfo.deviceName = GetDeviceName(lmsInfo.device);
    devInfo.expansionName = GetExpansionBoardName(lmsInfo.expansion);
    devInfo.firmwareVersion = std::to_string(int(lmsInfo.firmware));
    devInfo.hardwareVersion = std::to_string(int(lmsInfo.hardware));
    devInfo.protocolVersion = std::to_string(int(lmsInfo.protocol));
    devInfo.addrsLMS7002M.push_back(LMS7002M_SPI_INDEX);
    devInfo.addrSi5351 = Si5351_I2C_ADDR;
    devInfo.addrADF4002 = ADF4002_SPI_INDEX;
    devInfo.boardSerialNumber = lmsInfo.boardSerialNumber;
    return devInfo;
}

/** @brief Returns connected device information
*/
LMS64CProtocol::LMSinfo LMS64CProtocol::GetInfo()
{
    LMSinfo info;
    info.device = LMS_DEV_UNKNOWN;
    info.expansion = EXP_BOARD_UNKNOWN;
    info.firmware = 0;
    info.hardware = 0;
    info.protocol = 0;
    info.boardSerialNumber = 0;
    GenericPacket pkt;
    pkt.cmd = CMD_GET_INFO;
    int status = TransferPacket(pkt);
    if (status == 0 && pkt.inBuffer.size() >= 5)
    {
        info.firmware = pkt.inBuffer[0];
        info.device = pkt.inBuffer[1] < LMS_DEV_COUNT ? (eLMS_DEV)pkt.inBuffer[1] : LMS_DEV_UNKNOWN;
        info.protocol = pkt.inBuffer[2];
        info.hardware = pkt.inBuffer[3];
        info.expansion = pkt.inBuffer[4] < EXP_BOARD_COUNT ? (eEXP_BOARD)pkt.inBuffer[4] : EXP_BOARD_UNKNOWN;
        info.boardSerialNumber = (pkt.inBuffer[5] << 24) | (pkt.inBuffer[6] << 16) | (pkt.inBuffer[7] << 8) | pkt.inBuffer[8];
    }
    return info;
}

/** @brief Transfers data between packet and connected device
    @param pkt packet containing output data and to receive incomming data
    @return 0: success, other: failure
*/
int LMS64CProtocol::TransferPacket(GenericPacket& pkt)
{
    std::lock_guard<std::mutex> lock(mControlPortLock);
    int status = 0;
    if(IsOpen() == false) ReportError(ENOTCONN, "connection is not open");

    int packetLen;
    eLMS_PROTOCOL protocol = LMS_PROTOCOL_UNDEFINED;
    if(this->GetType() == SPI_PORT)
        protocol = LMS_PROTOCOL_NOVENA;
    else
        protocol = LMS_PROTOCOL_LMS64C;
    switch(protocol)
    {
    case LMS_PROTOCOL_UNDEFINED:
        return ReportError("protocol type undefined");
    case LMS_PROTOCOL_LMS64C:
        packetLen = ProtocolLMS64C::pktLength;
        break;
    case LMS_PROTOCOL_NOVENA:
        packetLen = pkt.outBuffer.size() > ProtocolNovena::pktLength ? ProtocolNovena::pktLength : pkt.outBuffer.size();
        break;
    default:
        packetLen = 0;
        return ReportError("Unknown protocol type %d", int(protocol));
    }
    int outLen = 0;
    unsigned char* outBuffer = NULL;
    outBuffer = PreparePacket(pkt, outLen, protocol);
    unsigned char* inBuffer = new unsigned char[outLen];
    memset(inBuffer, 0, outLen);

    int outBufPos = 0;
    int inDataPos = 0;
    if(outLen == 0)
    {
        //printf("packet outlen = 0\n");
        outLen = 1;
    }

    if(protocol == LMS_PROTOCOL_NOVENA)
    {
        bool transferData = true; //some commands are fake, so don't need transferring
        if(pkt.cmd == CMD_GET_INFO)
        {
            //spi does not have GET INFO, fake it to inform what device it is
            pkt.status = STATUS_COMPLETED_CMD;
            pkt.inBuffer.clear();
            pkt.inBuffer.resize(64, 0);
            pkt.inBuffer[0] = 0; //firmware
            pkt.inBuffer[1] = LMS_DEV_NOVENA; //device
            pkt.inBuffer[2] = 0; //protocol
            pkt.inBuffer[3] = 0; //hardware
            pkt.inBuffer[4] = EXP_BOARD_UNSUPPORTED; //expansion
            transferData = false;
        }

        if(transferData)
        {
            if (callback_logData)
                callback_logData(true, outBuffer, outLen);
            int bytesWritten = Write(outBuffer, outLen);
            if( bytesWritten == outLen)
            {
                if(pkt.cmd == CMD_LMS7002_RD)
                {
                    inDataPos = Read(&inBuffer[inDataPos], outLen);
                    if(inDataPos != outLen)
                        status = ReportError("Read(%d bytes) got %d", (int)outLen, (int)inDataPos);
                    else
                    {
                        if (callback_logData)
                            callback_logData(false, inBuffer, inDataPos);
                    }
                }
                ParsePacket(pkt, inBuffer, inDataPos, protocol);
            }
            else
                status = ReportError("Write(%d bytes) got %d", (int)outLen, (int)bytesWritten);
        }
    }
    else
    {
        for(int i=0; i<outLen; i+=packetLen)
        {
            int bytesToSend = packetLen;
            if (callback_logData)
                callback_logData(true, &outBuffer[outBufPos], bytesToSend);
            if( Write(&outBuffer[outBufPos], bytesToSend) )
            {
                outBufPos += packetLen;
                long readLen = packetLen;
                int bread = Read(&inBuffer[inDataPos], readLen);
                if(bread != readLen && protocol != LMS_PROTOCOL_NOVENA)
                {
                    status = ReportError("Read(%d bytes) failed", (int)readLen);
                    break;
                }
                if (callback_logData)
                    callback_logData(false, &inBuffer[inDataPos], bread);
                inDataPos += bread;
            }
            else
            {
                status = ReportError("Write(%d bytes) failed", (int)bytesToSend);
                break;
            }
        }
        ParsePacket(pkt, inBuffer, inDataPos, protocol);
    }
    delete outBuffer;
    delete inBuffer;
    return status;
}

/** @brief Takes generic packet and converts to specific protocol buffer
    @param pkt generic data packet to convert
    @param length returns length of returned buffer
    @param protocol which protocol to use for data
    @return pointer to data buffer, must be manually deleted after use
*/
unsigned char* LMS64CProtocol::PreparePacket(const GenericPacket& pkt, int& length, const eLMS_PROTOCOL protocol)
{
    unsigned char* buffer = NULL;
    if(protocol == LMS_PROTOCOL_UNDEFINED)
        return NULL;

    if(protocol == LMS_PROTOCOL_LMS64C)
    {
        ProtocolLMS64C packet;
        int maxDataLength = packet.maxDataLength;
        packet.cmd = pkt.cmd;
        packet.status = pkt.status;
        int byteBlockRatio = 1; //block ratio - how many bytes in one block
        switch( packet.cmd )
        {
        case CMD_PROG_MCU:
        case CMD_GET_INFO:
        case CMD_SI5351_RD:
        case CMD_SI5356_RD:
            byteBlockRatio = 1;
            break;
        case CMD_SI5351_WR:
        case CMD_SI5356_WR:
            byteBlockRatio = 2;
            break;
        case CMD_LMS7002_RD:
        case CMD_BRDSPI_RD:
        case CMD_BRDSPI8_RD:
            byteBlockRatio = 2;
            break;
        case CMD_ADF4002_WR:
            byteBlockRatio = 3;
            break;
        case CMD_LMS7002_WR:
        case CMD_BRDSPI_WR:
        case CMD_ANALOG_VAL_WR:
            byteBlockRatio = 4;
            break;
        default:
            byteBlockRatio = 1;
        }
        if (packet.cmd == CMD_LMS7002_RD || packet.cmd == CMD_BRDSPI_RD)
            maxDataLength = maxDataLength/2;
        if (packet.cmd == CMD_ANALOG_VAL_RD)
            maxDataLength = maxDataLength / 4;
        int blockCount = pkt.outBuffer.size()/byteBlockRatio;
        int bufLen = blockCount/(maxDataLength/byteBlockRatio)
                    +(blockCount%(maxDataLength/byteBlockRatio)!=0);
        bufLen *= packet.pktLength;
        if(bufLen == 0)
            bufLen = packet.pktLength;
        buffer = new unsigned char[bufLen];
        memset(buffer, 0, bufLen);
        int srcPos = 0;
        for(int j=0; j*packet.pktLength<bufLen; ++j)
        {
            int pktPos = j*packet.pktLength;
            buffer[pktPos] = packet.cmd;
            buffer[pktPos+1] = packet.status;
            if(blockCount > (maxDataLength/byteBlockRatio))
            {
                buffer[pktPos+2] = maxDataLength/byteBlockRatio;
                blockCount -= buffer[pktPos+2];
            }
            else
                buffer[pktPos+2] = blockCount;
            memcpy(&buffer[pktPos+3], packet.reserved, sizeof(packet.reserved));
            int bytesToPack = (maxDataLength/byteBlockRatio)*byteBlockRatio;
            for (int k = 0; k<bytesToPack && srcPos < pkt.outBuffer.size(); ++srcPos, ++k)
                buffer[pktPos + 8 + k] = pkt.outBuffer[srcPos];
        }
        length = bufLen;
    }
    else if(protocol == LMS_PROTOCOL_NOVENA)
    {
        if(pkt.cmd == CMD_LMS7002_RST)
        {
            buffer = new unsigned char[8];
            buffer[0] = 0x88;
            buffer[1] = 0x06;
            buffer[2] = 0x00;
            buffer[3] = 0x18;
            buffer[4] = 0x88;
            buffer[5] = 0x06;
            buffer[6] = 0x00;
            buffer[7] = 0x38;
            length = 8;
        }
        else
        {
            buffer = new unsigned char[pkt.outBuffer.size()];
            memcpy(buffer, &pkt.outBuffer[0], pkt.outBuffer.size());
            if (pkt.cmd == CMD_LMS7002_WR)
            {
                for(int i=0; i<pkt.outBuffer.size(); i+=4)
                    buffer[i] |= 0x80;
            }
            length = pkt.outBuffer.size();
        }
    }
    return buffer;
}

/** @brief Parses given data buffer into generic packet
    @param pkt destination packet
    @param buffer received data from board
    @param length received buffer length
    @param protocol which protocol to use for data parsing
    @return 1:success, 0:failure
*/
int LMS64CProtocol::ParsePacket(GenericPacket& pkt, const unsigned char* buffer, const int length, const eLMS_PROTOCOL protocol)
{
    if(protocol == LMS_PROTOCOL_UNDEFINED)
        return -1;

    if(protocol == LMS_PROTOCOL_LMS64C)
    {
        ProtocolLMS64C packet;
        int inBufPos = 0;
        pkt.inBuffer.resize(packet.maxDataLength*(length / packet.pktLength + (length % packet.pktLength)), 0);
        for(int i=0; i<length; i+=packet.pktLength)
        {
            pkt.cmd = (eCMD_LMS)buffer[i];
            pkt.status = (eCMD_STATUS)buffer[i+1];
            memcpy(&pkt.inBuffer[inBufPos], &buffer[i+8], packet.maxDataLength);
            inBufPos += packet.maxDataLength;
        }
    }
    else if(protocol == LMS_PROTOCOL_NOVENA)
    {
        pkt.cmd = CMD_LMS7002_RD;
        pkt.status = STATUS_COMPLETED_CMD;
        pkt.inBuffer.clear();
        for(int i=0; i<length; i+=2)
        {
            //reading from spi returns only registers values
            //fill addresses as zeros to match generic format of address, value pairs
            pkt.inBuffer.push_back(0); //should be address msb
            pkt.inBuffer.push_back(0); //should be address lsb
            pkt.inBuffer.push_back(buffer[i]);
            pkt.inBuffer.push_back(buffer[i+1]);
        }
    }
    return 1;
}

int LMS64CProtocol::ProgramWrite(const char *data_src, const size_t length, const int prog_mode, const int device, ProgrammingCallback callback)
{
#ifndef NDEBUG
    auto t1 = std::chrono::high_resolution_clock::now();
#endif
    char progressMsg[128];
    bool abortProgramming = false;
    int bytesSent = 0;

    bool needsData = true;
    if(device == FPGA && prog_mode == 2)
        needsData = false;
    if(device == FX3 && (prog_mode == 0 || prog_mode == 1))
        needsData = false;

    if(length == 0 && needsData)
    {
        return ReportError(EIO, "ProgramWrite length should be > 0");
    }

    if (not this->IsOpen())
    {
        return ReportError(ENOTCONN, "connection is not open");
    }

    const int pktSize = 32;
    int data_left = length;
    const int portionsCount = length/pktSize + (length%pktSize > 0) + 1; // +1 programming end packet
    int portionNumber;
    int status = 0;
    eCMD_LMS cmd;
    if(device != FPGA)
        cmd = CMD_MEMORY_WR;
    else if(device == FPGA)
        cmd = CMD_ALTERA_FPGA_GW_WR;
    else
    {
        sprintf(progressMsg, "Programming failed! Target device not supported");
        if(callback)
            abortProgramming = callback(bytesSent, length, progressMsg);
        return ReportError(progressMsg);
    }

    unsigned char ctrbuf[64];
    unsigned char inbuf[64];
    memset(ctrbuf, 0, 64);
    ctrbuf[0] = cmd;
    ctrbuf[1] = 0;
    ctrbuf[2] = 56;

    for (portionNumber = 0; portionNumber<portionsCount && !abortProgramming; ++portionNumber)
    {
        int offset = 8;
        memset(&ctrbuf[offset], 0, 56);
        ctrbuf[offset+0] = prog_mode;
        ctrbuf[offset+1] = (portionNumber >> 24) & 0xFF;
        ctrbuf[offset+2] = (portionNumber >> 16) & 0xFF;
        ctrbuf[offset+3] = (portionNumber >> 8) & 0xFF;
        ctrbuf[offset+4] = portionNumber & 0xFF;
        unsigned char data_cnt = data_left > pktSize ? pktSize : data_left;
        ctrbuf[offset+5] = data_cnt;
        if(cmd == CMD_MEMORY_WR)
        {
            ctrbuf[offset+6] = 0;
            ctrbuf[offset+7] = 0;
            ctrbuf[offset+8] = 0;
            ctrbuf[offset+9] = 0;

            ctrbuf[offset+10] = (device >> 8) & 0xFF;
            ctrbuf[offset+11] = device & 0xFF;
        }
        if(data_src != NULL)
        {
            memcpy(&ctrbuf[offset + 24], data_src, data_cnt);
            data_src += data_cnt;
        }

        if(Write(ctrbuf, sizeof(ctrbuf)) != sizeof(ctrbuf))
        {
            if(callback)
                callback(bytesSent, length, "Programming failed! Write operation failed");
            return ReportError("Programming failed! Write operation failed");
        }
        if(Read(inbuf, sizeof(inbuf)) != sizeof(ctrbuf))
        {
            if(callback)
                callback(bytesSent, length, "Programming failed! Read operation failed");
            return ReportError("Programming failed! Read operation failed");
        }
        data_left -= data_cnt;
        status = inbuf[1];
        bytesSent += data_cnt;

        if(status != STATUS_COMPLETED_CMD)
        {
            sprintf(progressMsg, "Programming failed! %s", status2string(status));
            if(callback)
                abortProgramming = callback(bytesSent, length, progressMsg);
#ifndef NDEBUG
            printf("\n%s\n", progressMsg);
#endif
            return ReportError(EPROTO);
        }
        if(needsData == false) //only one packet is needed to initiate bitstream from flash
        {
            bytesSent = length;
            break;
        }
        sprintf(progressMsg, "programing: %6i/%i", portionNumber, portionsCount - 1);
        if(callback)
            abortProgramming = callback(bytesSent, length, progressMsg);
#ifndef NDEBUG
        printf("%s\r", progressMsg);
#endif
    }
    if (abortProgramming == true)
    {
        sprintf(progressMsg, "programming: aborted by user");
#ifndef NDEBUG
        printf("\n%s\n", progressMsg);
#endif
        if(callback)
            callback(bytesSent, length, progressMsg);
        return ReportError(ECONNABORTED, "user aborted programming");
    }
    sprintf(progressMsg, "programming: completed");
    if(callback)
        callback(bytesSent, length, progressMsg);
#ifndef NDEBUG
    auto t2 = std::chrono::high_resolution_clock::now();
	if ((device == 2 && prog_mode == 2) == false)
        printf("\nProgramming finished, %li bytes sent! %li ms\n", length, std::chrono::duration_cast<std::chrono::milliseconds>(t2 - t1).count());
	else
		printf("\nFPGA configuring initiated\n");
#endif
    return 0;
}

int LMS64CProtocol::CustomParameterRead(const uint8_t *ids, double *values, const int count, std::string* units)
{
    LMS64CProtocol::GenericPacket pkt;
    pkt.cmd = CMD_ANALOG_VAL_RD;

    for (int i=0; i<count; ++i)
        pkt.outBuffer.push_back(ids[i]);

    int status = this->TransferPacket(pkt);
    if (status != 0) return convertStatus(status, pkt);

    assert(pkt.inBuffer.size() >= 4 * count);

    for (int i = 0; i < count; ++i)
    {
        int unitsIndex = (pkt.inBuffer[i * 4 + 1] & 0xF0) >> 4;
        if(units)
            units[i] = adcUnits2string(unitsIndex);
        values[i] = pkt.inBuffer[i * 4 + 2] << 8 | pkt.inBuffer[i * 4 + 3];
        int powerOf10 = pkt.inBuffer[i * 4 + 1] & 0x0F;
        values[i] *= pow(10, powerOf10);
        if(unitsIndex == TEMPERATURE)
            values[i] /= 10;
    }
    return 0;
}

int LMS64CProtocol::CustomParameterWrite(const uint8_t *ids, const double *values, const int count, const std::string* units)
{
    LMS64CProtocol::GenericPacket pkt;
    pkt.cmd = CMD_ANALOG_VAL_WR;

    for (int i = 0; i < count; ++i)
    {
        pkt.outBuffer.push_back(ids[i]);
        int powerOf10 = 0;
        if(values[i] != 0)
            powerOf10 = log10(values[i])/3;
        int unitsId = 0; // need to convert given units to their enum
        pkt.outBuffer.push_back(unitsId << 4 | powerOf10);
        int value = values[i] / pow(10, 3*powerOf10);
        pkt.outBuffer.push_back(value >> 8);
        pkt.outBuffer.push_back(value & 0xFF);
    }
    int status = this->TransferPacket(pkt);
    return convertStatus(status, pkt);
}
