myriadrf/front-end-modules/LimeSDR_PA_LNA/gui/src/splash_image.h

/* splash.png - 8875 bytes */
static const unsigned char splash_png[] = {
  0x89, 0x50, 0x4e, 0x47, 0x0d, 0x0a, 0x1a, 0x0a,
  0x00, 0x00, 0x00, 0x0d, 0x49, 0x48, 0x44, 0x52,
  0x00, 0x00, 0x00, 0xc3, 0x00, 0x00, 0x00, 0x6a,
  0x08, 0x02, 0x00, 0x00, 0x00, 0x8e, 0x0e, 0x72,
  0xdb, 0x00, 0x00, 0x22, 0x72, 0x49, 0x44, 0x41,
  0x54, 0x78, 0xda, 0xed, 0x5d, 0x07, 0x78, 0x54,
  0x45, 0xdb, 0xdd, 0x9a, 0x4d, 0xef, 0x21, 0xbd,
  0x82, 0x80, 0xf4, 0xd0, 0x8b, 0x82, 0x28, 0x88,
  0x34, 0x11, 0x91, 0x5e, 0x05, 0x15, 0x3b, 0x58,
  0x50, 0x44, 0xd0, 0x4f, 0x51, 0x90, 0xa6, 0x14,
  0x41, 0x40, 0x45, 0x6a, 0xa4, 0x8a, 0x08, 0x08,
  0x48, 0x51, 0x91, 0x92, 0xd0, 0x13, 0x4c, 0x20,
  0x94, 0xf4, 0xde, 0x7b, 0xb6, 0xef, 0x7f, 0xf6,
  0xbe, 0x30, 0xdf, 0xfd, 0x76, 0x43, 0xd8, 0x90,
  0x35, 0xc5, 0xff, 0xbe, 0x4f, 0x9e, 0x3c, 0xf7,
  0xce, 0x9d, 0x3e, 0x67, 0xce, 0x7b, 0x66, 0x6e,
  0x59, 0xb1, 0xc1, 0x60, 0x10, 0x09, 0x26, 0x58,
  0xad, 0x4d, 0x2c, 0x20, 0x49, 0x30, 0xab, 0x98,
  0x80, 0x24, 0xc1, 0xac, 0x63, 0x02, 0x92, 0x04,
  0xb3, 0x8e, 0xd5, 0x0c, 0x49, 0x95, 0x5a, 0x65,
  0xb9, 0xaa, 0xdc, 0xd3, 0xc1, 0xa3, 0xbe, 0xab,
  0x2d, 0x58, 0x83, 0xb3, 0x9a, 0x21, 0x49, 0x6f,
  0xd0, 0xff, 0x9e, 0x78, 0xa6, 0xb9, 0x67, 0x58,
  0xa0, 0xb3, 0x5f, 0x7d, 0xd7, 0x5c, 0xb0, 0x86,
  0x65, 0x35, 0xf6, 0x6e, 0x65, 0xea, 0xf2, 0x6d,
  0x31, 0x7b, 0xc7, 0xb7, 0x1b, 0xee, 0x68, 0xe3,
  0x50, 0xdf, 0x95, 0x17, 0xac, 0x01, 0xd9, 0x83,
  0xe8, 0xa4, 0x8b, 0x19, 0x31, 0x3f, 0x5f, 0x3f,
  0xf2, 0xe9, 0xe3, 0xef, 0x88, 0x45, 0x92, 0xfa,
  0xae, 0xbf, 0x60, 0x0d, 0xc5, 0x1e, 0x50, 0x71,
  0x2f, 0x3e, 0xbd, 0x46, 0x21, 0x55, 0xcc, 0xe8,
  0x3e, 0xad, 0xbe, 0xeb, 0x2f, 0x58, 0x43, 0xb1,
  0x07, 0x44, 0x92, 0x56, 0xaf, 0x7d, 0x6e, 0xe7,
  0x4b, 0x2f, 0x76, 0x1c, 0x3f, 0xb8, 0xf9, 0x13,
  0xf5, 0xdd, 0x04, 0xc1, 0x1a, 0x84, 0x3d, 0xf8,
  0x2e, 0xc0, 0xd9, 0xd4, 0x8b, 0x6f, 0x1e, 0x9a,
  0xf7, 0xfd, 0xb0, 0xa5, 0xed, 0xbc, 0x5b, 0xd5,
  0x77, 0x2b, 0x04, 0xab, 0x7f, 0xab, 0xd5, 0x7e,
  0xd2, 0x9c, 0x63, 0x0b, 0x0f, 0xdc, 0x3c, 0x7e,
  0xf2, 0xf9, 0x3d, 0xae, 0xb6, 0x2e, 0xf5, 0xdd,
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
